Quicr/hactar/models/debug_board_case/debug-board-case-top.step

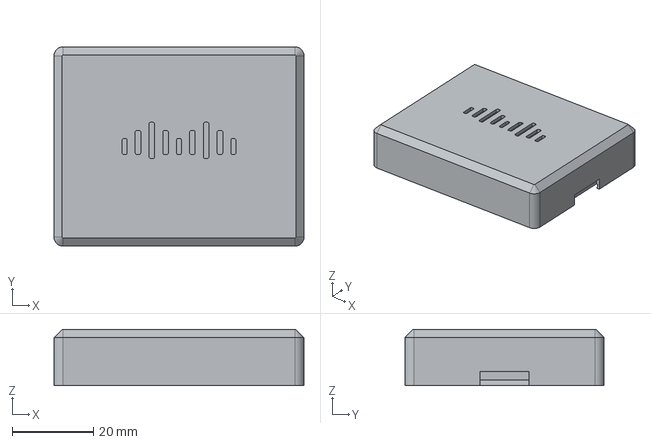
[picture p20: CAD file, 2026-09-29]
models/debug_board_case/debug-board-case-top.step
61.6 x 49.1 x 13.8 mm
