Quicr/hactar/models/ev15v2/ev15-case-topPad051.step

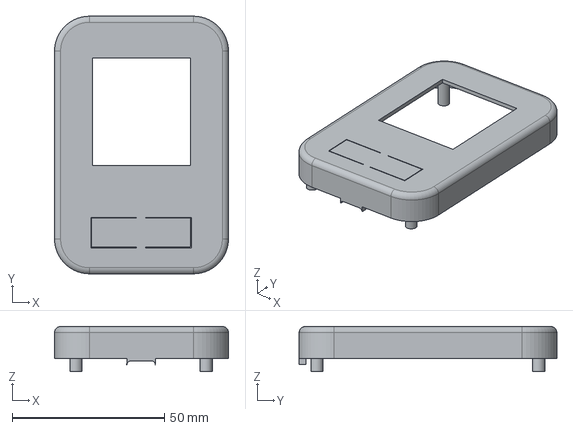
[picture p21: CAD file, 2026-01-12]
models/ev15v2/ev15-case-topPad051.step
57.2 x 84.7 x 14.8 mm
