Quicr/hactar/models/ev15v2/front-buttons-steps/ev15-case-front-button.step

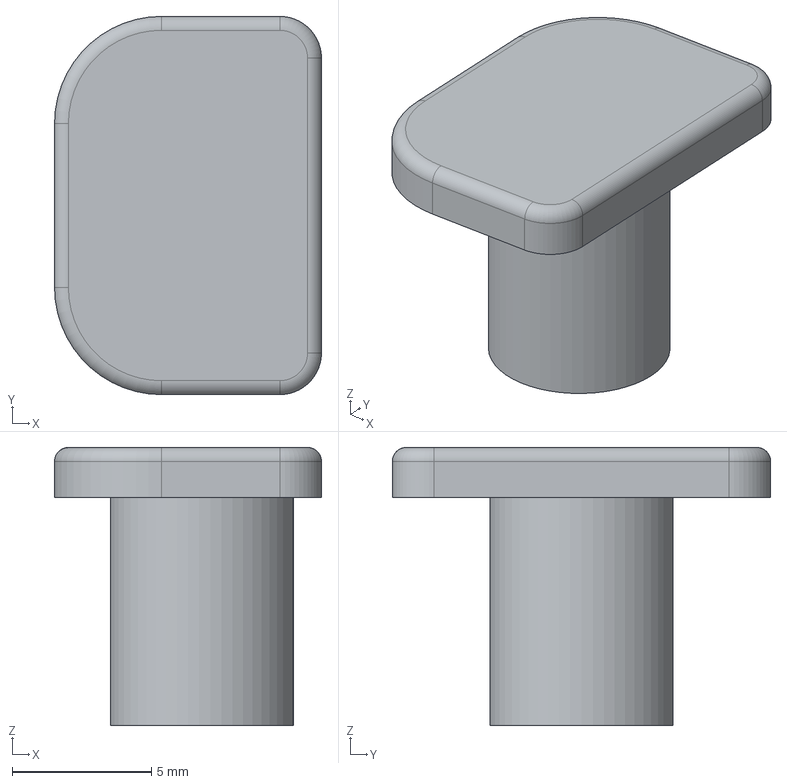
[picture p22: CAD file, 2025-11-21]
models/ev15v2/front-buttons-steps/ev15-case-front-button.step
9.60 x 13.6 x 10.0 mm
