Quicr/hactar/models/ev16/ev16-case-top.step

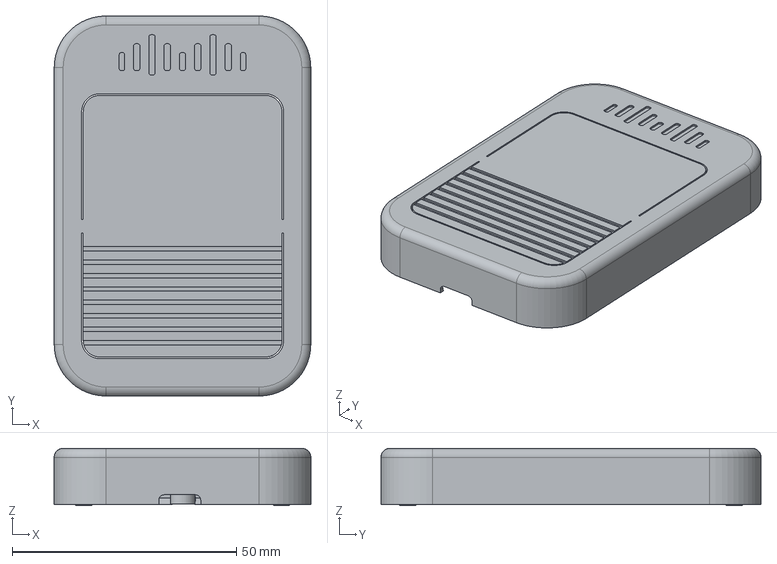
[picture p23: CAD file, 2026-01-12]
models/ev16/ev16-case-top.step
57.2 x 84.7 x 12.8 mm
