Quicr/hactar/models/ev17/ev17-case-top.step

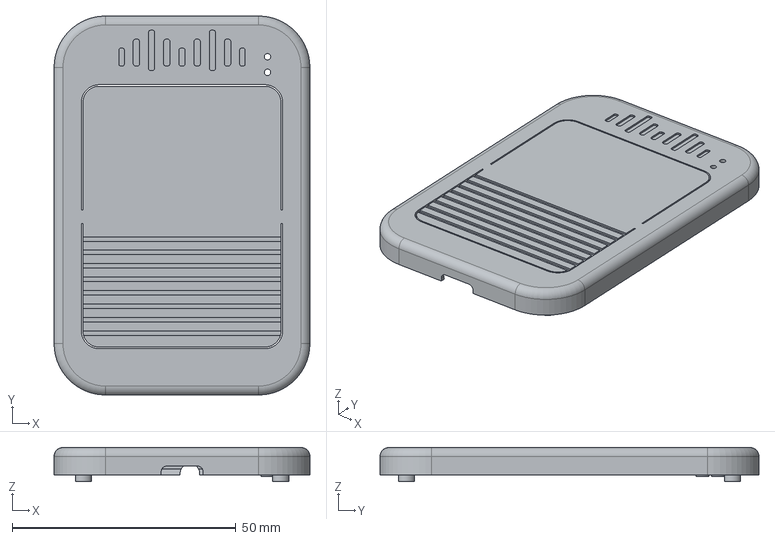
[picture p24: CAD file, 2026-05-21]
models/ev17/ev17-case-top.step
57.2 x 84.7 x 7.60 mm
