Quicr/hactar/models/ev19/keytar/ev19-keytar-case-inner-shelf.step

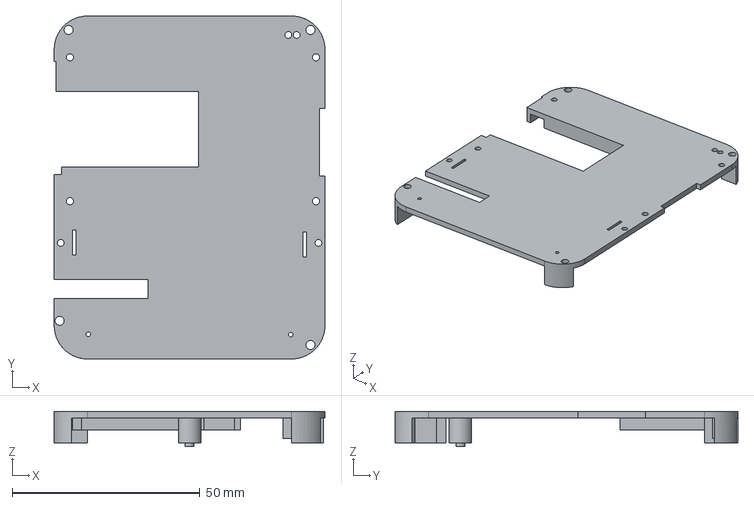
[picture p25: CAD file, 2026-09-29]
models/ev19/keytar/ev19-keytar-case-inner-shelf.step
72.1 x 91.3 x 9.40 mm
