Quicr/hactar/models/debug_board_case/debug-board-case-bottom.step

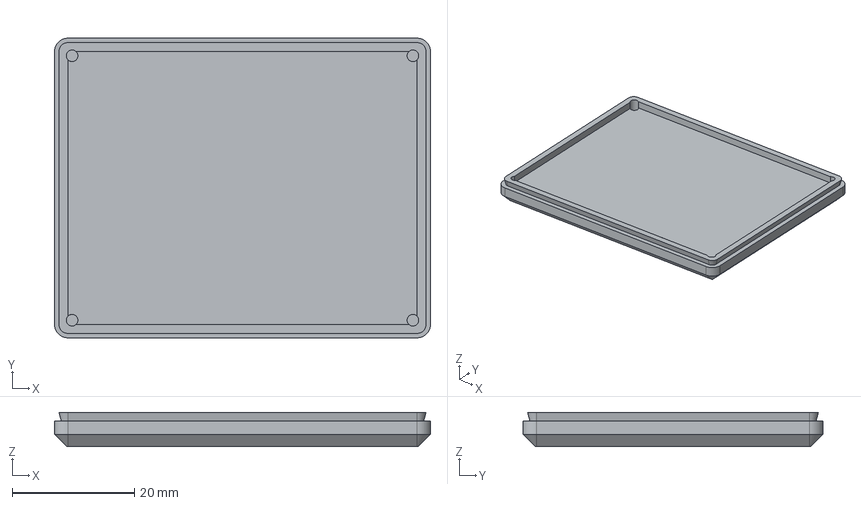
[picture p26: CAD file, 2026-09-29]
models/debug_board_case/debug-board-case-bottom.step
61.6 x 49.1 x 5.60 mm
