Quicr/hactar/models/ev15/brett_model/demo/ev15-case-screen-platform.step

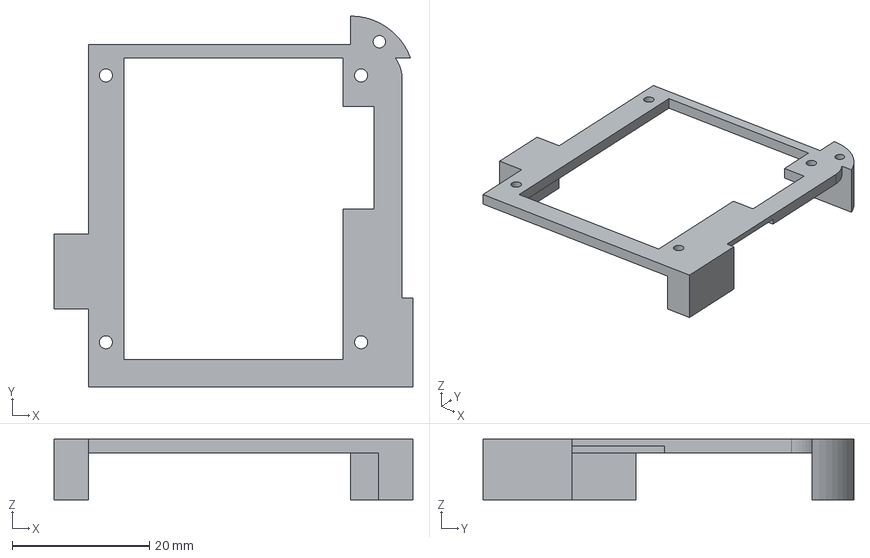
[picture p27: CAD file, 2025-11-21]
models/ev15/brett_model/demo/ev15-case-screen-platform.step
52.4 x 54.1 x 8.85 mm
