Quicr/hactar/models/ev15v2/front-buttons-steps/ev15-case-front-button-cap_+0.05mm.step

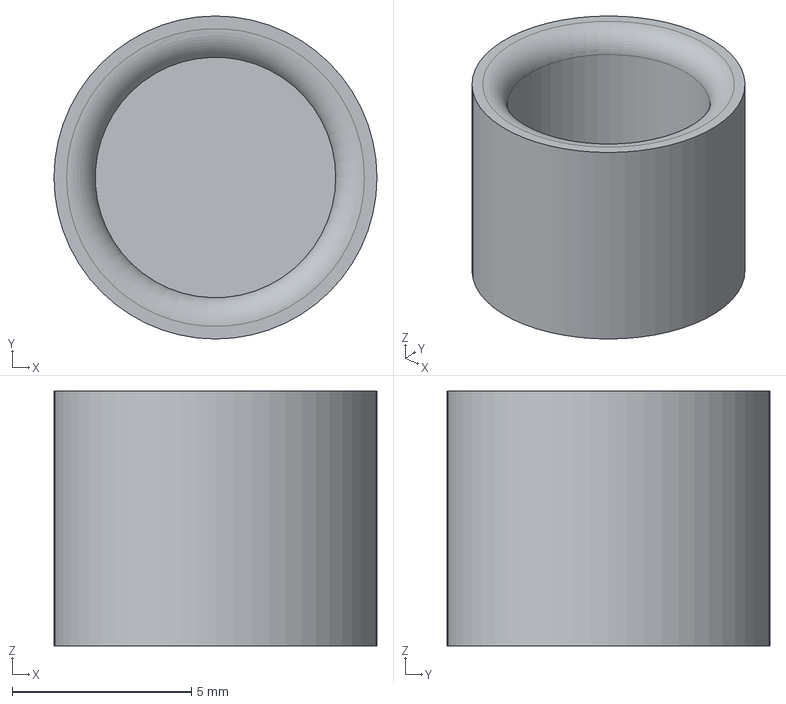
[picture p28: CAD file, 2025-11-21]
models/ev15v2/front-buttons-steps/ev15-case-front-button-cap_+0.05mm.step
9.00 x 9.00 x 7.10 mm
