Quicr/hactar/models/ev16/ev16-case-side-buttons.step

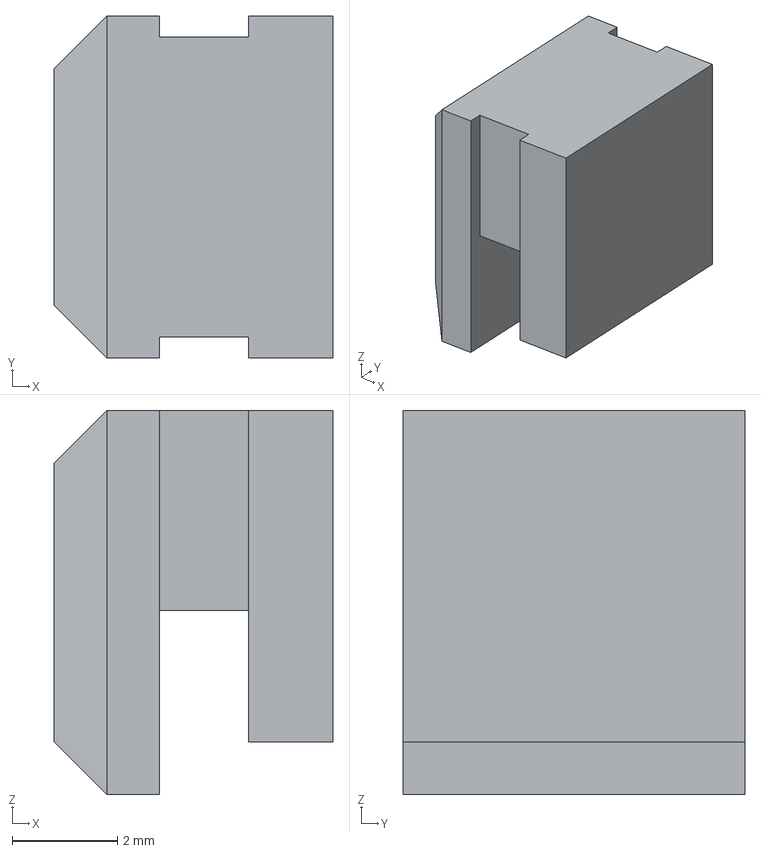
[picture p29: CAD file, 2026-01-12]
models/ev16/ev16-case-side-buttons.step
5.30 x 6.50 x 7.31 mm
