Quicr/hactar/models/ev17/ev17-case-side-buttons.step

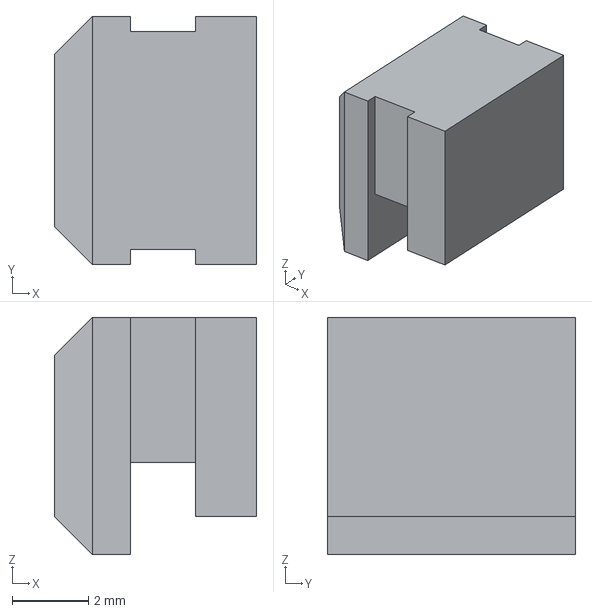
[picture p30: CAD file, 2026-05-21]
models/ev17/ev17-case-side-buttons.step
5.30 x 6.50 x 6.20 mm
