Quicr/hactar/models/ev19/keytar/ev19-keytar-case.FCStd

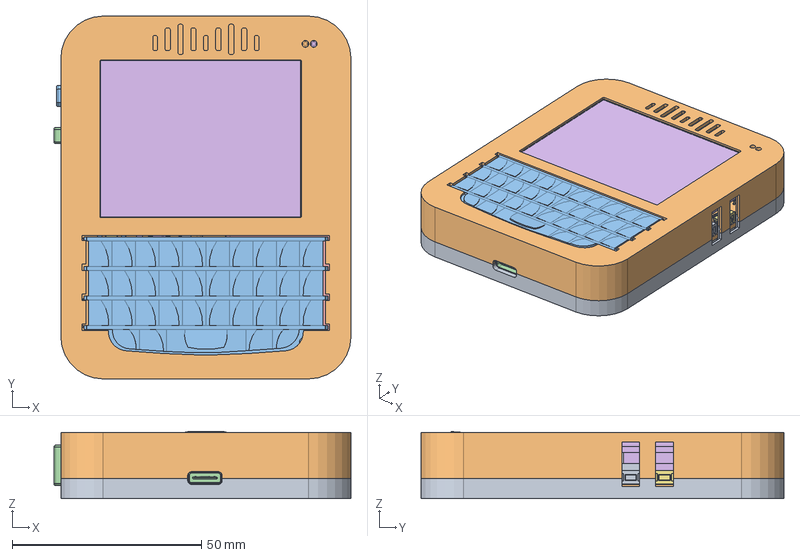
[picture p31: CAD file, 2026-09-29]
models/ev19/keytar/ev19-keytar-case.FCStd
78.5 x 95.9 x 17.7 mm
bottom
top
power-switch
side-button
screen-body
TSSOP-8_4.4x3mm_P0.65mm
C_0805_2012Metric
R_1206_3216Metric
R_0402_1005Metric
R_0402_1005Metric002
R_0402_1005Metric004
R_0402_1005Metric006
R_1206_3216Metric002
SOT-23
C_0402_1005Metric
C_0402_1005Metric002
R_1206_3216Metric004
ESP32-S3-WROOM-1
USB-C_SMD-TYPE-C-31-M-12
LQFP-48_7x7mm_P0.5mm
R_0402_1005Metric008
R_0402_1005Metric010
R_0402_1005Metric012
SOT-23-6
C_0402_1005Metric004
R_0402_1005Metric014
LED-ARRAY-SMD_4P-L1.6-W1.5-TL_NH-B1515RGBA
C_0402_1005Metric006
C_0402_1005Metric008
C_0805_2012Metric002
R_0402_1005Metric016
R_0402_1005Metric018
R_0402_1005Metric020
C_0402_1005Metric010
R_0402_1005Metric022
R_0402_1005Metric024
R_0402_1005Metric026
C_0402_1005Metric012
C_0805_2012Metric004
C_0402_1005Metric014
SOT-23-5
R_0402_1005Metric028
R_1206_3216Metric006
R_0402_1005Metric030
R_0402_1005Metric032
USB-C_SMD-TYPE-C-31-M-002
C_0805_2012Metric006
R_0402_1005Metric034
R_0402_1005Metric036
R_0402_1005Metric038
R_0603_1608Metric
R_0402_1005Metric040
R_0402_1005Metric042
R_0402_1005Metric044
R_0402_1005Metric046
C_0805_2012Metric008
R_0402_1005Metric048
C_0402_1005Metric016
R_1206_3216Metric008
R_0402_1005Metric050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
