Quicr/hactar/models/ev15/brett_model/demo/ev15-case-front-button.step

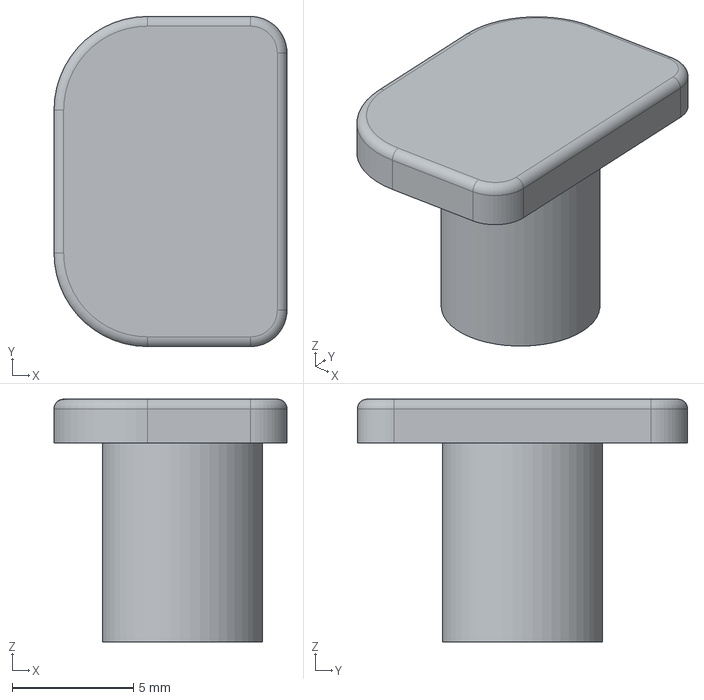
[picture p32: CAD file, 2025-11-21]
models/ev15/brett_model/demo/ev15-case-front-button.step
9.60 x 13.6 x 10.0 mm
