Quicr/hactar/models/ev17/ev17-case-bottom.step

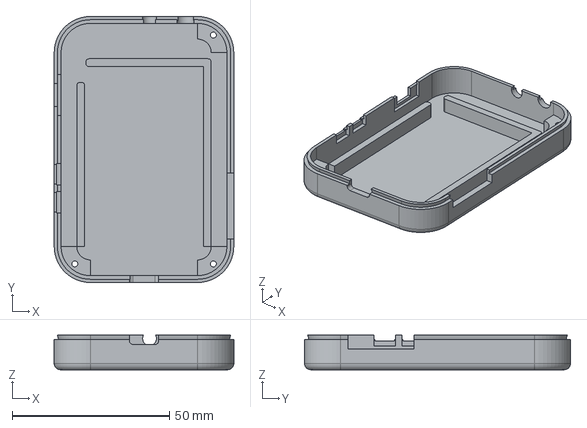
[picture p33: CAD file, 2026-05-21]
models/ev17/ev17-case-bottom.step
57.2 x 84.7 x 11.0 mm
