Quicr/hactar/models/ev19/keytar/ev19-keytar-case-top-debug-hole.step

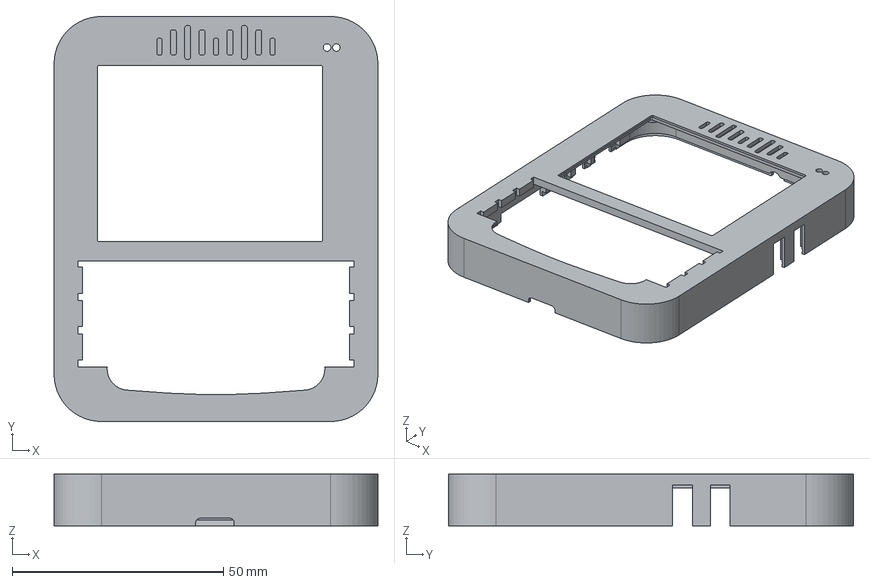
[picture p34: CAD file, 2026-09-29]
models/ev19/keytar/ev19-keytar-case-top-debug-hole.step
76.7 x 95.9 x 12.2 mm
