Quicr/hactar/models/ev17/ev17-case-power-switch.step

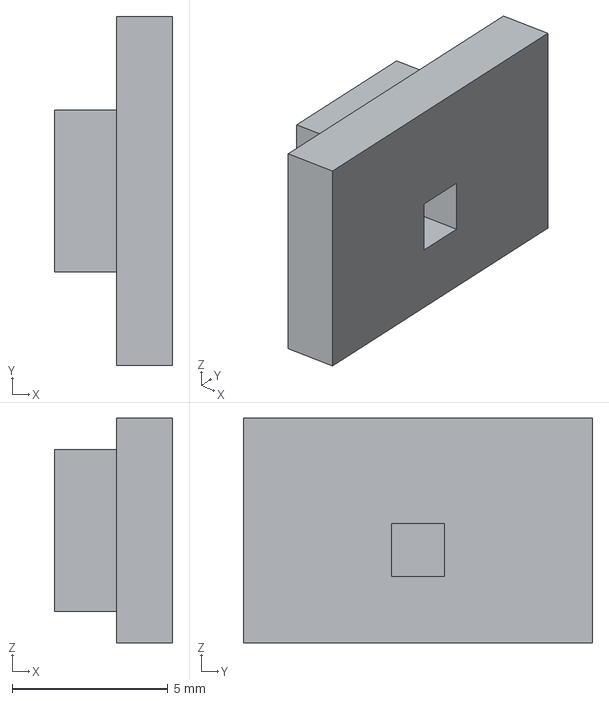
[picture p35: CAD file, 2026-05-21]
models/ev17/ev17-case-power-switch.step
3.80 x 11.2 x 7.21 mm
