Quicr/hactar/models/ev19/keytar/ev19-keytar-case-top.step

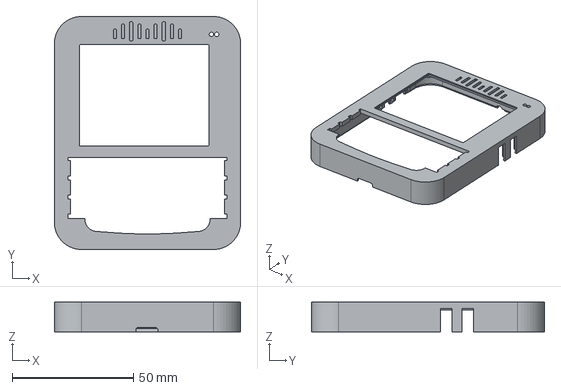
[picture p36: CAD file, 2026-09-29]
models/ev19/keytar/ev19-keytar-case-top.step
76.7 x 95.9 x 12.2 mm
