Quicr/hactar/models/ev19/keytar/ev19-keytar-case-bottom.step

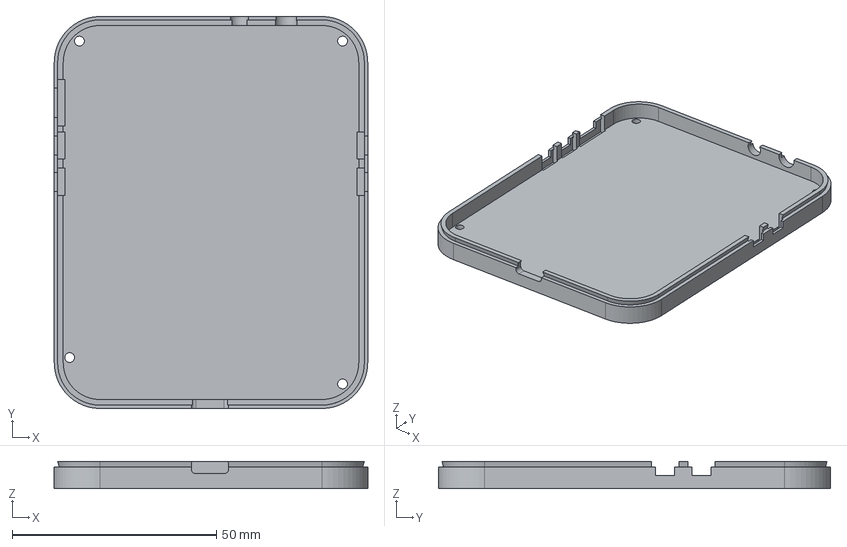
[picture p37: CAD file, 2026-09-29]
models/ev19/keytar/ev19-keytar-case-bottom.step
76.7 x 95.9 x 6.70 mm
