Quicr/hactar/models/ev19/keytar/ev19-keytar-case-power-switch.step

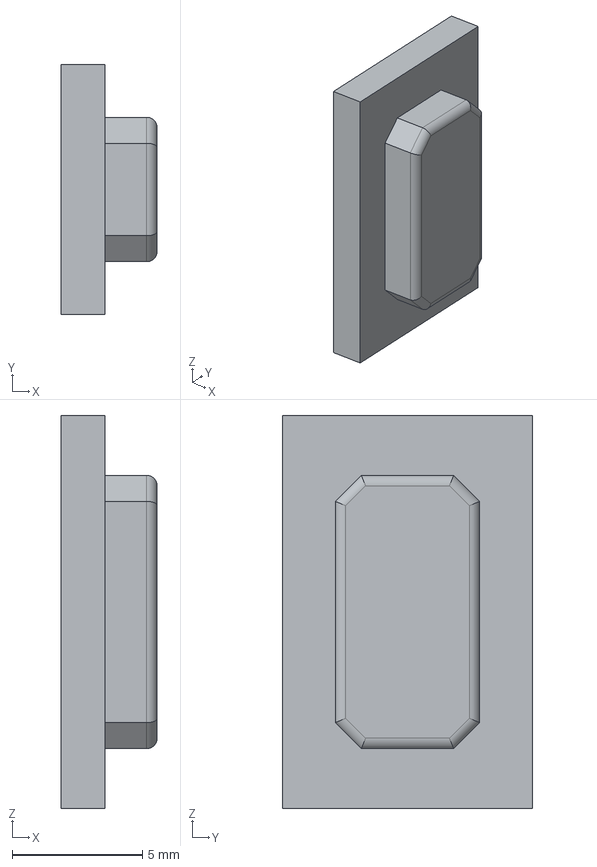
[picture p38: CAD file, 2026-09-29]
models/ev19/keytar/ev19-keytar-case-power-switch.step
3.70 x 9.60 x 15.1 mm
