Quicr/hactar/models/ev19/keytar/ev19-keytar-keyboard-shim.step

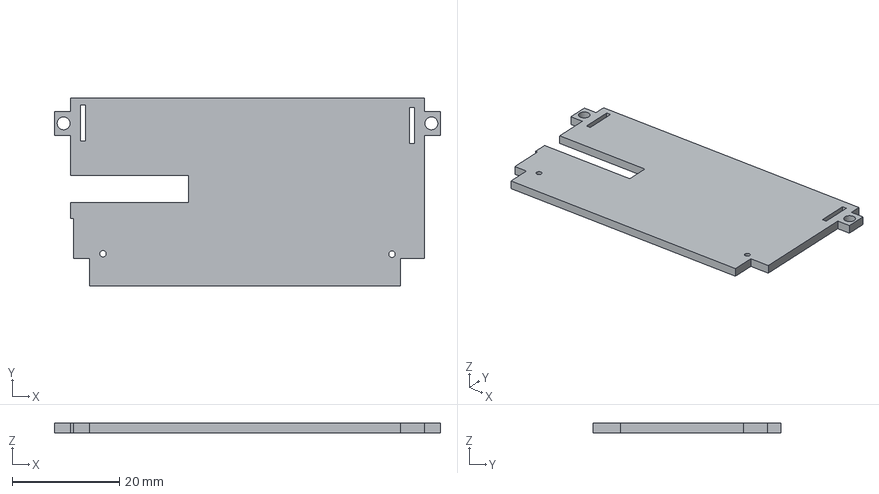
[picture p39: CAD file, 2026-09-29]
models/ev19/keytar/ev19-keytar-keyboard-shim.step
72.0 x 35.1 x 1.80 mm
