Quicr/hactar/firmware/mgmt/Core/Inc/io_control.h

#ifndef IO_CONTROL_H
#define IO_CONTROL_H

#include "main.h"
#include "uart_stream.h"

#define BAUD 115200


void PowerCycle(GPIO_TypeDef* port, uint16_t pin, uint32_t delay);
void HoldInReset(GPIO_TypeDef* port, uint16_t pin);
void ChangeToInput(GPIO_TypeDef* port, uint16_t pin);
void ChangeToOutput(GPIO_TypeDef* port, uint16_t pin);
void NormalAndNetUploadUartInit(uart_stream_t* stream, UART_HandleTypeDef* tx_uart);
void UIUploadStreamInit(uart_stream_t* stream, UART_HandleTypeDef* tx_uart);

#endif
