Quicr/hactar/firmware/net/components/serial/serial.cc

#include "serial.hh"
#include "logger.hh"
#include <random>

// This code is VERY specifically using espressif's serial event system which
// has many flaws, including but not limited to taking forever and less
// granularity.

Serial::Serial(const uart_port_t port,
               uart_dev_t& uart,
               const periph_interrupt_t intr_source,
               const uart_config_t uart_config,
               const int tx_pin,
               const int rx_pin,
               const int rts_pin,
               const int cts_pin,
               uint8_t& tx_buff,
               const uint32_t tx_buff_sz,
               uint8_t& rx_buff,
               const uint32_t rx_buff_sz,
               const uint32_t rx_rings,
               const uint32_t driver_tx_size,
               const uint32_t driver_rx_size,
               const uint32_t driver_queue_size,
               const bool use_queue_task,
               const bool use_slip) :
    SerialHandler(rx_rings, tx_buff, tx_buff_sz, rx_buff, rx_buff_sz, Transmit, this),
    port(port),
    uart(uart),
    read_handle(nullptr),
    uart_config(uart_config),
    tx_pin(tx_pin),
    rx_pin(rx_pin),
    rts_pin(rts_pin),
    cts_pin(cts_pin),
    driver_tx_size(driver_tx_size),
    driver_rx_size(driver_rx_size),
    driver_queue_size(driver_queue_size),
    use_queue_task(use_queue_task),
    queue(),
    uart_task_handle(nullptr)
{
}

void Serial::BeginEventTask(TaskHandle_t& read_handle)
{
    ESP_ERROR_CHECK(uart_param_config(port, &uart_config));
    ESP_ERROR_CHECK(uart_set_pin(port, tx_pin, rx_pin, rts_pin, cts_pin));

    this->read_handle = &read_handle;

    if (use_queue_task)
    {
        ESP_ERROR_CHECK(uart_driver_install(port, driver_rx_size, driver_tx_size, driver_queue_size,
                                            &queue, 0));
        xTaskCreate(QueueReadTask, "UART Queue Event Task", 4096, this, 20, &uart_task_handle);
    }
    else
    {
        ESP_ERROR_CHECK(uart_driver_install(port, driver_rx_size, driver_tx_size, driver_queue_size,
                                            nullptr, 0));
        xTaskCreate(ReadTask, "UART Read Event Task", 4096, this, 20, &uart_task_handle);
    }
}

Serial::~Serial()
{
    if (uart_task_handle)
    {
        vTaskDelete(uart_task_handle);
    }

    if (use_queue_task)
    {
        uart_driver_delete(port);
    }
}

void Serial::UpdateUnread(const uint16_t update)
{
    unread -= update;
}

void Serial::Transmit(void* arg)
{
    // TODO semaphores?
    Serial* serial = static_cast<Serial*>(arg);
    uart_write_bytes(serial->port, serial->tx_buff + serial->tx_read_idx, serial->num_to_send);
    serial->tx_free = true;
    serial->UpdateTx();
}

void Serial::ReadTask(void* arg)
{
    Serial* serial = static_cast<Serial*>(arg);

    while (true)
    {
        // Check if buffer is full
        if (serial->unread >= serial->rx_buff_sz)
        {
            vTaskDelay(1);
            continue;
        }

        // Calculate space to end of buffer (for contiguous write)
        int space_to_end = serial->rx_buff_sz - serial->rx_write_idx;
        // Calculate total free space in circular buffer
        int free_space = serial->rx_buff_sz - serial->unread;
        // Limit to contiguous space available
        int bytes_to_read = (space_to_end < free_space) ? space_to_end : free_space;

        if (bytes_to_read <= 0)
        {
            vTaskDelay(1);
            continue;
        }

        int num_bytes = uart_read_bytes(serial->port, serial->rx_buff + serial->rx_write_idx,
                                        bytes_to_read, 20 / portTICK_PERIOD_MS);

        if (num_bytes <= 0)
        {
            continue;
        }

        serial->rx_write_idx += num_bytes;
        if (serial->rx_write_idx >= serial->rx_buff_sz)
        {
            serial->rx_write_idx = 0;
        }
        serial->unread += num_bytes;
        xTaskNotifyGive(*serial->read_handle);
    }
}

void Serial::QueueReadTask(void* arg)
{
    Serial* serial = static_cast<Serial*>(arg);
    uart_event_t event;

    while (true)
    {
        if (!xQueueReceive(serial->queue, &event, portMAX_DELAY))
        {
            continue;
        }

        // NET_LOG_INFO("got event, size %d", event.size);

        switch (event.type)
        {
        case UART_DATA:
        {
            int bytes_remaining = event.size;
            int total_read = 0;

            while (bytes_remaining > 0)
            {
                // Check if buffer is full
                if (serial->unread >= serial->rx_buff_sz)
                {
                    ESP_LOGW("SerialPort", "RX buffer full, dropping %d bytes", bytes_remaining);
                    uart_flush_input(serial->port);
                    break;
                }

                // Calculate space to end of buffer (for contiguous write)
                int space_to_end = serial->rx_buff_sz - serial->rx_write_idx;
                // Calculate total free space in circular buffer
                int free_space = serial->rx_buff_sz - serial->unread;
                // Limit to contiguous space available
                int space_available = (space_to_end < free_space) ? space_to_end : free_space;
                // Don't read more than remaining bytes in event
                int bytes_to_read =
                    (space_available < bytes_remaining) ? space_available : bytes_remaining;

                if (bytes_to_read <= 0)
                {
                    break;
                }

                int num_bytes = uart_read_bytes(
                    serial->port, serial->rx_buff + serial->rx_write_idx, bytes_to_read, 0);

                if (num_bytes <= 0)
                {
                    break;
                }

                total_read += num_bytes;
                bytes_remaining -= num_bytes;
                serial->unread += num_bytes;

                serial->rx_write_idx += num_bytes;
                if (serial->rx_write_idx >= serial->rx_buff_sz)
                {
                    serial->rx_write_idx = 0;
                }
            }

            if (total_read > 0)
            {
                xTaskNotifyGive(*serial->read_handle);
            }

            break;
        }
        case UART_FIFO_OVF:
        {

            ESP_LOGW("SerialPort", "FIFO Overflow detected");
            uart_flush_input(serial->port);
            xQueueReset(serial->queue);
            break;
        }
        case UART_BUFFER_FULL:
        {
            ESP_LOGW("SerialPort", "Ring buffer full");
            uart_flush_input(serial->port);
            xQueueReset(serial->queue);
            break;
        }
        case UART_PARITY_ERR:
        {

            ESP_LOGE("SerialPort", "Parity error");
            break;
        }
        case UART_FRAME_ERR:
        {

            ESP_LOGE("SerialPort", "Frame error");
            break;
        }
        default:
        {
            ESP_LOGI("SerialPort", "Unhandled UART event type: %d", event.type);
            break;
        }
        }
    }
}
