Quicr/hactar/firmware/net/core/src/mgmt_link_handler.cc

#include "mgmt_link_handler.hh"
#include "efuse_burner.hh"
#include "esp_system.h"
#include "freertos/FreeRTOS.h"
#include "logger.hh"
#include "net.hh"
#include "net_mgmt_link.h"
#include "picoquic_utils.h"
#include "spdlog/spdlog.h"
#include "ui_net_link.hh"
#include <cstdint>

void MgmtLinkHandler::BlasterTask(void* arg)
{
    BlasterTaskContext* context = static_cast<BlasterTaskContext*>(arg);

    std::vector<uint8_t> blast_vec;
    constexpr uint8_t channel_id = (uint8_t)ui_net_link::Channel_Id::Ptt;
    TickType_t last_wake = xTaskGetTickCount();
    const TickType_t frequency = pdMS_TO_TICKS(20);
    if (context->blaster.enabled)
    {

        if (context->blaster.packet_size != blast_vec.size())
        {
            blast_vec.resize(context->blaster.packet_size);
            for (int i = 0; i < context->blaster.packet_size; ++i)
            {
                blast_vec[i] = 0;
            }
        }

        context->moq_context.PushAudioFrame(channel_id, blast_vec.data(), blast_vec.size(),
                                            context->runtime.curr_audio_isr_time);
    }

    xTaskDelayUntil(&last_wake, frequency);

    vTaskDelete(context->blaster.task_handle);
    context->blaster.task_handle = NULL;
}

MgmtLinkHandler::MgmtLinkHandler(Serial& mgmt_layer,
                                 Serial& ui_layer,
                                 Wifi& wifi,
                                 Storage& storage,
                                 ConfigState& config,
                                 Diagnostics& diagnostics,
                                 MoqContext& moq_context,
                                 Runtime& runtime_context) :
    serial(mgmt_layer),
    ui_serial(ui_layer),
    wifi(wifi),
    storage(storage),
    config(config),
    diagnostics(diagnostics),
    moq_context(moq_context),
    runtime_context(runtime_context),
    serial_read_handle(nullptr),
    serial_read_buffer(),
    serial_read_stack(),
    serial_read_semaphore(nullptr),
    serial_read_running(false),
    blaster_context(ui_layer, mgmt_layer, moq_context, runtime_context, diagnostics.blaster)
{
}

MgmtLinkHandler::~MgmtLinkHandler()
{
    serial_read_running = false;

    if (serial_read_handle)
    {
        // Tell the task to wake up so it can be stopped
        xTaskNotifyGive(serial_read_handle);
        xSemaphoreTake(serial_read_semaphore, portMAX_DELAY);
        serial_read_handle = nullptr;
    }

    if (serial_read_semaphore)
    {
        vSemaphoreDelete(serial_read_semaphore);
        serial_read_semaphore = nullptr;
    }

    if (serial_read_stack)
    {
        heap_caps_free(serial_read_stack);
        serial_read_stack = nullptr;
    }
}

void MgmtLinkHandler::Begin()
{
    CreateLinkPacketTask();
    serial.BeginEventTask(serial_read_handle);
}

void MgmtLinkHandler::CreateLinkPacketTask()
{
    NET_LOG_INFO("Creating mgmt link packet task");

    serial_read_semaphore = xSemaphoreCreateBinary();
    if (serial_read_semaphore == NULL)
    {
        esp_system_abort("Failed to allocate semaphore for mgmt link packet handler");
        return;
    }

    serial_read_stack =
        (StackType_t*)heap_caps_malloc(Stack_Size * sizeof(StackType_t), MALLOC_CAP_INTERNAL);
    if (serial_read_stack == NULL)
    {
        esp_system_abort("Failed to allocate stack for mgmt link packet handler");
        return;
    }

    serial_read_running = true;
    serial_read_handle = xTaskCreateStatic(LinkPacketTask, "mgmt link packet handler", Stack_Size,
                                           this, 10, serial_read_stack, &serial_read_buffer);

    NET_LOG_INFO("Created mgmt link packet handler Internal RAM left %ld",
                 heap_caps_get_free_size(MALLOC_CAP_INTERNAL));
}

void MgmtLinkHandler::LinkPacketTask(void* arg)
{
    MgmtLinkHandler* handler = static_cast<MgmtLinkHandler*>(arg);

    NET_LOG_INFO("Start mgmt link packet task");
    while (handler->serial_read_running)
    {
        ulTaskNotifyTake(pdTRUE, portMAX_DELAY);

        while (auto packet = handler->serial.Read())
        {
            switch (static_cast<CtlToNet>(packet->type))
            {
            case CtlToNet::Ping:
            {
                handler->serial.Reply(
                    static_cast<uint16_t>(NetToCtl::Pong),
                    std::span<const uint8_t>(packet->payload.data(), packet->length));
                break;
            }
            case CtlToNet::CircularPing:
            {
                // Forward to UI for circular path: MGMT -> NET -> UI -> MGMT
                handler->ui_serial.Reply(
                    static_cast<uint16_t>(ui_net_link::NetToUi::CircularPing),
                    std::span<const uint8_t>(packet->payload.data(), packet->length));
                break;
            }
            case CtlToNet::ClearStorage:
            {
                if (ESP_OK != handler->storage.Clear())
                {
                    handler->serial.ReplyError(static_cast<uint16_t>(NetToCtl::Error),
                                               "Storage clear failed");
                    break;
                }

                // Clear in-memory caches (NVS already wiped by storage.Clear())
                handler->config.moq_server_url.stored.clear();
                handler->config.user_id = 0;
                handler->config.user_name.stored.clear();
                handler->config.language.stored.clear();
                handler->config.channel_ns_json.stored.clear();
                handler->config.ai_query_ns_json.stored.clear();
                handler->config.ai_audio_response_ns_json.stored.clear();
                handler->config.ai_cmd_response_ns_json.stored.clear();

                // Clear in-memory namespace vectors
                handler->config.channel_ns.clear();
                handler->config.ai_query_ns.clear();
                handler->config.ai_audio_response_ns.clear();
                handler->config.ai_cmd_response_ns.clear();

                handler->wifi.ClearSavedSSIDs();

                handler->serial.Reply(static_cast<uint16_t>(NetToCtl::Ack),
                                      std::span<const uint8_t>{});
                break;
            }
            case CtlToNet::AddWifiSsid:
            {
                try
                {
                    std::string json_str((char*)packet->payload.data(), packet->length);
                    json wifi_json = json::parse(json_str);

                    if (!wifi_json.contains("ssid") || !wifi_json.contains("password"))
                    {
                        NET_LOG_ERROR("Add_Wifi: missing ssid or password field");
                        handler->serial.ReplyError(static_cast<uint16_t>(NetToCtl::Error),
                                                   "Missing ssid or password field");
                        break;
                    }

                    std::string ssid = wifi_json["ssid"].get<std::string>();
                    std::string password = wifi_json["password"].get<std::string>();

                    NET_LOG_INFO("Add_Wifi: ssid=%s", ssid.c_str());
                    handler->wifi.Connect(ssid, password);
                    handler->serial.Reply(static_cast<uint16_t>(NetToCtl::Ack),
                                          std::span<const uint8_t>{});
                }
                catch (const std::exception& ex)
                {
                    NET_LOG_ERROR("Add_Wifi: JSON parse error: %s", ex.what());
                    handler->serial.ReplyError(static_cast<uint16_t>(NetToCtl::Error),
                                               "Invalid JSON");
                }
                break;
            }
            case CtlToNet::GetWifiSsids:
            {
                json wifi_array = json::array();
                const std::vector<Wifi::ap_cred_t>& creds = handler->wifi.GetStoredCreds();
                for (const auto& cred : creds)
                {
                    json entry;
                    entry["ssid"] = std::string(cred.name, cred.name_len);
                    entry["password"] = std::string(cred.pwd, cred.pwd_len);
                    wifi_array.push_back(entry);
                }
                handler->serial.Reply(static_cast<uint16_t>(NetToCtl::WifiSsids),
                                      wifi_array.dump());
                break;
            }
            case CtlToNet::ClearWifiSsids:
            {
                handler->wifi.ClearSavedSSIDs();
                handler->serial.Reply(static_cast<uint16_t>(NetToCtl::Ack),
                                      std::span<const uint8_t>{});
                break;
            }
            case CtlToNet::SetRelayUrl:
            {
                std::string moq_url((char*)packet->payload.data(), packet->length);
                NET_LOG_INFO("Got moq url %d - %s", moq_url.length(), moq_url.c_str());

                if (moq_url.length() == 0)
                {
                    NET_LOG_INFO("Cleaning moq url because length is zero");
                    handler->config.moq_server_url.Clear();
                    handler->serial.Reply(static_cast<uint16_t>(NetToCtl::Ack),
                                          std::span<const uint8_t>{});
                    break;
                }
                handler->config.moq_server_url = moq_url;
                handler->serial.Reply(static_cast<uint16_t>(NetToCtl::Ack),
                                      std::span<const uint8_t>{});
                break;
            }
            case CtlToNet::GetRelayUrl:
            {
                std::string moq_url = handler->config.moq_server_url.Load();
                handler->serial.Reply(static_cast<uint16_t>(NetToCtl::RelayUrl), moq_url);
                break;
            }
            case CtlToNet::GetLoopback:
            {
                uint8_t mode = static_cast<uint8_t>(handler->diagnostics.loopback);
                handler->serial.Reply(static_cast<uint16_t>(NetToCtl::Loopback),
                                      std::span<const uint8_t>(&mode, 1));
                break;
            }
            case CtlToNet::SetLoopback:
            {
                if (packet->length < 1)
                {
                    handler->serial.ReplyError(static_cast<uint16_t>(NetToCtl::Error),
                                               "Missing loopback mode parameter");
                    break;
                }
                auto mode = static_cast<NetLoopbackMode>(packet->payload[0]);
                switch (mode)
                {
                case NetLoopbackMode::Off:
                    handler->diagnostics.loopback = NetLoopbackMode::Off;
                    NET_LOG_INFO("Loopback set to: off");
                    handler->serial.Reply(static_cast<uint16_t>(NetToCtl::Ack),
                                          std::span<const uint8_t>{});
                    break;
                case NetLoopbackMode::Raw:
                    handler->diagnostics.loopback = NetLoopbackMode::Raw;
                    NET_LOG_INFO("Loopback set to: raw");
                    handler->serial.ReplyError(static_cast<uint16_t>(NetToCtl::Ack),
                                               "Raw loopback not supported");
                    break;
                case NetLoopbackMode::Moq:
                    handler->diagnostics.loopback = NetLoopbackMode::Moq;
                    NET_LOG_INFO("Loopback set to: moq");
                    handler->serial.Reply(static_cast<uint16_t>(NetToCtl::Ack),
                                          std::span<const uint8_t>{});
                    break;
                default:
                    NET_LOG_WARN("Unknown loopback mode: %d", static_cast<int>(mode));
                    handler->serial.ReplyError(static_cast<uint16_t>(NetToCtl::Error),
                                               "Unknown loopback mode");
                    break;
                }
                break;
            }
            case CtlToNet::GetLogsEnabled:
            {
                uint8_t enabled = handler->diagnostics.logs_disabled ? 0 : 1;
                handler->serial.Reply(static_cast<uint16_t>(NetToCtl::LogsEnabled),
                                      std::span<const uint8_t>(&enabled, 1));
                break;
            }
            case CtlToNet::SetLogsEnabled:
            {
                if (packet->length < 1)
                {
                    handler->serial.ReplyError(static_cast<uint16_t>(NetToCtl::Error),
                                               "Missing logs enabled parameter");
                    break;
                }
                uint8_t enabled = packet->payload[0];
                if (enabled)
                {
                    handler->EnableLogging();
                }
                else
                {
                    handler->DisableLogging();
                }
                handler->serial.Reply(static_cast<uint16_t>(NetToCtl::Ack),
                                      std::span<const uint8_t>{});
                break;
            }
            case CtlToNet::SetLanguage:
            {
                std::string new_lang((char*)packet->payload.data(), packet->length);
                if (!ConfigState::IsValidLanguage(new_lang))
                {
                    NET_LOG_ERROR("Invalid language: %s", new_lang.c_str());
                    handler->serial.ReplyError(static_cast<uint16_t>(NetToCtl::Error),
                                               "Invalid language");
                    break;
                }
                handler->config.language = new_lang;
                NET_LOG_INFO("Language set to: %s", new_lang.c_str());
                handler->serial.Reply(static_cast<uint16_t>(NetToCtl::Ack),
                                      std::span<const uint8_t>{});
                handler->moq_context.UpdateAITracks(handler->config);
                handler->moq_context.UpdateChannelTracks(handler->config);
                break;
            }
            case CtlToNet::GetLanguage:
            {
                std::string lang = handler->config.language.Load();
                handler->serial.Reply(static_cast<uint16_t>(NetToCtl::Language), lang);
                break;
            }
            case CtlToNet::SetChannel:
            {
                std::string json_str((char*)packet->payload.data(), packet->length);
                auto parsed = ConfigState::JsonToNamespace(json_str);
                if (!parsed.has_value())
                {
                    NET_LOG_ERROR("Failed to parse channel namespace JSON");
                    handler->serial.ReplyError(static_cast<uint16_t>(NetToCtl::Error),
                                               "Invalid channel namespace JSON");
                    break;
                }

                handler->config.channel_ns = parsed.value();
                handler->config.channel_ns_json = json_str;
                NET_LOG_INFO("Channel namespace set (%zu parts)",
                             handler->config.channel_ns.size());
                handler->serial.Reply(static_cast<uint16_t>(NetToCtl::Ack),
                                      std::span<const uint8_t>{});
                handler->moq_context.UpdateChannelTracks(handler->config);
                break;
            }
            case CtlToNet::GetChannel:
            {
                handler->serial.Reply(static_cast<uint16_t>(NetToCtl::Channel),
                                      handler->config.channel_ns_json.Load());
                break;
            }
            case CtlToNet::GetAi:
            {
                json response;
                response["query"] = handler->config.ai_query_ns;
                response["audio"] = handler->config.ai_audio_response_ns;
                response["cmd"] = handler->config.ai_cmd_response_ns;
                handler->serial.Reply(static_cast<uint16_t>(NetToCtl::Ai), response.dump());
                break;
            }
            case CtlToNet::SetAi:
            {
                std::string json_str((char*)packet->payload.data(), packet->length);
                try
                {
                    json ai_config = json::parse(json_str);
                    if (!ai_config.is_object() || !ai_config.contains("query")
                        || !ai_config.contains("audio") || !ai_config.contains("cmd"))
                    {
                        NET_LOG_ERROR("AI config must be object with query, audio, cmd fields");
                        handler->serial.ReplyError(static_cast<uint16_t>(NetToCtl::Error),
                                                   "AI config requires query, audio, cmd fields");
                        break;
                    }

                    auto query_parsed = ConfigState::JsonToNamespace(ai_config["query"].dump());
                    auto audio_parsed = ConfigState::JsonToNamespace(ai_config["audio"].dump());
                    auto cmd_parsed = ConfigState::JsonToNamespace(ai_config["cmd"].dump());

                    if (!query_parsed || !audio_parsed || !cmd_parsed)
                    {
                        NET_LOG_ERROR("Failed to parse AI namespace arrays");
                        handler->serial.ReplyError(static_cast<uint16_t>(NetToCtl::Error),
                                                   "Invalid AI namespace arrays");
                        break;
                    }

                    handler->config.ai_query_ns = query_parsed.value();
                    handler->config.ai_audio_response_ns = audio_parsed.value();
                    handler->config.ai_cmd_response_ns = cmd_parsed.value();

                    handler->config.ai_query_ns_json = ai_config["query"].dump();
                    handler->config.ai_audio_response_ns_json = ai_config["audio"].dump();
                    handler->config.ai_cmd_response_ns_json = ai_config["cmd"].dump();

                    NET_LOG_INFO("AI namespaces set (query=%zu, audio=%zu, cmd=%zu parts)",
                                 handler->config.ai_query_ns.size(),
                                 handler->config.ai_audio_response_ns.size(),
                                 handler->config.ai_cmd_response_ns.size());
                    handler->serial.Reply(static_cast<uint16_t>(NetToCtl::Ack),
                                          std::span<const uint8_t>{});
                    handler->moq_context.UpdateAITracks(handler->config);
                }
                catch (const std::exception& ex)
                {
                    NET_LOG_ERROR("Failed to parse AI config JSON: %s", ex.what());
                    handler->serial.ReplyError(static_cast<uint16_t>(NetToCtl::Error),
                                               "Invalid AI config JSON");
                }
                break;
            }
            case CtlToNet::BlasterSend:
            {
                handler->serial.Reply(static_cast<uint16_t>(NetToCtl::Ack),
                                      std::span<const uint8_t>{});
                break;
            }
            case CtlToNet::GetBlaster:
            {
                const uint8_t get_blaster[3] = {
                    handler->diagnostics.blaster.enabled,
                    static_cast<uint8_t>(handler->diagnostics.blaster.packet_size & 0xFF),
                    static_cast<uint8_t>(handler->diagnostics.blaster.packet_size >> 8),
                };

                handler->serial.Reply(
                    static_cast<uint16_t>(NetToCtl::Blaster),
                    std::span<const uint8_t>(reinterpret_cast<const uint8_t*>(&get_blaster),
                                             sizeof(get_blaster)));

                break;
            }
            case CtlToNet::SetBlaster:
            {
                if (packet->length < 3)
                {
                    handler->serial.ReplyError(static_cast<uint16_t>(NetToCtl::Error),
                                               "SetBlaster requires {enabled:1}{size:2}");
                    break;
                }

                handler->diagnostics.blaster.enabled = packet->payload[0];

                const int16_t packet_size = (static_cast<uint16_t>(packet->payload[1]) & 0xFF)
                                          | (static_cast<uint16_t>(packet->payload[2] << 8));

                if (packet_size > 0)
                {
                    handler->diagnostics.blaster.packet_size = packet_size;
                }

                handler->serial.Reply(static_cast<uint16_t>(NetToCtl::Ack),
                                      std::span<const uint8_t>{});

                if (handler->diagnostics.blaster.enabled
                    && handler->diagnostics.blaster.task_handle == nullptr)
                {
                    xTaskCreate(BlasterTask, "Blaster task", 4096, (void*)&handler->blaster_context,
                                10, &handler->diagnostics.blaster.task_handle);
                }
                break;
            }
            case CtlToNet::BurnJtagEfuse:
            {
                const bool res = BurnDisableUSBJTagEFuse();
                if (res)
                {
                    handler->serial.Reply(static_cast<uint16_t>(NetToCtl::Ack),
                                          std::span<const uint8_t>{});
                }
                else
                {
                    handler->serial.ReplyError(static_cast<uint16_t>(NetToCtl::Error),
                                               "eFuse burn failed");
                }
                break;
            }
            case CtlToNet::GetUserId:
            {
                handler->config.user_id.Load();
                const uint64_t user_id = handler->config.user_id;
                handler->serial.Reply(
                    static_cast<uint16_t>(NetToCtl::UserId),
                    std::span<const uint8_t>(reinterpret_cast<const uint8_t*>(&user_id),
                                             sizeof(user_id)));
                break;
            }
            case CtlToNet::SetUserId:
            {
                if (packet->length != sizeof(handler->config.user_id.stored))
                {
                    break;
                }

                uint64_t user_id = 0;
                memcpy(&user_id, packet->payload.data(), sizeof(user_id));

                handler->config.user_id = user_id;

                NET_LOG_INFO("User id set to %lld", user_id);

                handler->serial.Reply(static_cast<uint16_t>(NetToCtl::Ack),
                                      std::span<const uint8_t>{});

                break;
            }
            case CtlToNet::GetUserName:
            {
                std::string username = handler->config.user_name.Load();
                handler->serial.Reply(static_cast<uint16_t>(NetToCtl::UserName), username);
                break;
            }
            case CtlToNet::SetUserName:
            {

                std::string new_name((char*)packet->payload.data(), packet->length);
                handler->config.user_name = new_name;
                NET_LOG_INFO("Language set to: %s", new_name.c_str());

                handler->serial.Reply(static_cast<uint16_t>(NetToCtl::Ack),
                                      std::span<const uint8_t>{});
                handler->moq_context.UpdateAITracks(handler->config);
                handler->moq_context.UpdateChannelTracks(handler->config);
                break;
            }
            default:
            {
                handler->serial.ReplyError(static_cast<uint16_t>(NetToCtl::Error),
                                           "Unknown packet type");
                NET_LOG_ERROR("Unknown packet type 0x%04x from mgmt", packet->type);
                break;
            }
            }
        }
    }

    xSemaphoreGive(handler->serial_read_semaphore);
    vTaskDelete(NULL);
}

void MgmtLinkHandler::DisableLogging()
{
    esp_log_level_set("*", ESP_LOG_NONE);
    auto logger = spdlog::get("MTC");
    if (logger)
    {
        diagnostics.last_spd_log_level = logger->level();
        logger->set_level(spdlog::level::level_enum::off);
    }

    debug_printf_suspend();
    diagnostics.logs_disabled = true;
}

void MgmtLinkHandler::EnableLogging()
{
    // Renable
    esp_log_level_set("*", ESP_LOG_MAX);

    auto logger = spdlog::get("MTC");
    if (logger)
    {
        logger->set_level(diagnostics.last_spd_log_level);
    }

    debug_printf_resume();
    diagnostics.logs_disabled = false;
}
