Quicr/hactar/firmware/net/components/moq_manager/moq_session.cc

#include "moq_session.hh"
#include "logger.hh"
#include "peripherals.hh"
#include "task_helpers.hh"
#include "utils.hh"
#include <driver/gpio.h>

using namespace moq;

extern uint64_t device_id;

Session::Session(const quicr::ClientConfig& cfg,
                 std::vector<std::shared_ptr<TrackReader>>& readers,
                 std::vector<std::shared_ptr<TrackWriter>>& writers) :
    Client(cfg),
    readers(readers),
    readers_task_handle(),
    readers_task_buffer(),
    readers_task_stack(),
    writers(writers),
    writers_task_handle(),
    writers_task_buffer(),
    writers_task_stack(),
    readers_mux(),
    writers_mux()
{
    StartTasks();
}

void Session::StopTracks() noexcept
{
    for (const auto& reader : readers)
    {
        if (reader)
        {
            UnsubscribeTrack(reader);
        }
    }

    for (const auto& writer : writers)
    {
        if (writer)
        {
            UnpublishTrack(writer);
        }
    }
}

void Session::StartTasks() noexcept
{
    task_helpers::Start_PSRAM_Task(PublishTrackTask, this, "Publish Tracks task",
                                   writers_task_handle, writers_task_buffer, &writers_task_stack,
                                   8192, 10);
    task_helpers::Start_PSRAM_Task(SubscribeTrackTask, this, "Subscribe Tracks task",
                                   readers_task_handle, readers_task_buffer, &readers_task_stack,
                                   8192, 10);
}

void Session::StatusChanged(Status status)
{
    switch (status)
    {
    case Status::kReady:
        Logger::Log(Logger::Level::Info, "MOQ Connection ready");
        gpio_set_level(NET_LED_G, 1);
        gpio_set_level(NET_LED_B, 0);
        break;
    case Status::kConnecting:
        break;
    case Status::kPendingServerSetup:
        Logger::Log(Logger::Level::Info, "MOQ Connection connected and now pending server setup");
        break;
    default:
        Logger::Log(Logger::Level::Error, "MOQ Connection failed: %i", static_cast<int>(status));
        break;
    }
}

std::shared_ptr<TrackWriter> Session::Writer(const size_t id) noexcept
{
    if (id > writers.size())
    {
        NET_LOG_ERROR("ERROR, writer with id %ld does not exist", id);
        return nullptr;
    }

    return writers[id];
}

void Session::PublishTrackTask(void* params)
{
    // TODO use a mutex to try and subscribe/publish
    // as I could remove them from the list or update them.
    Session* session = static_cast<Session*>(params);

    while (true)
    {
        while (session->GetStatus() != moq::Session::Status::kReady)
        {
            vTaskDelay(100 / portTICK_PERIOD_MS);
            continue;
        }

        {
            std::lock_guard<std::mutex> _(session->writers_mux);

            for (auto& writer : session->writers)
            {
                if (!writer)
                {
                    continue;
                }

                const auto can_publish = [&] {
                    const auto status = writer->GetStatus();
                    return status == moq::TrackWriter::Status::kOk
                        || status == moq::TrackWriter::Status::kSubscriptionUpdated
                        || status == moq::TrackWriter::Status::kNewGroupRequested;
                };

                // Writer is publishing
                if (can_publish())
                {
                    continue;
                }

                session->PublishTrack(writer);

                while (!can_publish())
                {
                    vTaskDelay(300 / portTICK_PERIOD_MS);
                }
            }
        }

        vTaskDelay(5000 / portTICK_PERIOD_MS);
    }

    vTaskDelete(nullptr);
}

void Session::SubscribeTrackTask(void* params)
{
    // TODO use a mutex to try and subscribe/publish
    // as I could remove them from the list or update them.

    // TODO notifier that awakes the thread when a new sub or pub is available
    Session* session = static_cast<Session*>(params);

    while (true)
    {
        while (session->GetStatus() != moq::Session::Status::kReady)
        {
            vTaskDelay(100 / portTICK_PERIOD_MS);
            continue;
        }

        {
            std::lock_guard<std::mutex> _(session->readers_mux);

            for (auto& reader : session->readers)
            {
                if (!reader)
                {
                    continue;
                }

                // Reader is subscribed
                if (reader->GetStatus() == moq::TrackReader::Status::kOk)
                {
                    continue;
                }

                session->SubscribeTrack(reader);

                while (reader->GetStatus() != moq::TrackReader::Status::kOk)
                {
                    vTaskDelay(300 / portTICK_PERIOD_MS);
                }
            }
        }

        vTaskDelay(5000 / portTICK_PERIOD_MS);
    }

    vTaskDelete(nullptr);
}

// TODO delete when moq session can be reused instead of reinstantiated
std::unique_lock<std::mutex> Session::GetReaderLock()
{
    return std::unique_lock<std::mutex>(readers_mux);
}

std::unique_lock<std::mutex> Session::GetWriterLock()
{
    return std::unique_lock<std::mutex>(writers_mux);
}
