Quicr/hactar/firmware/net/core/src/peripherals.cc

#include "peripherals.hh"
#include "driver/gpio.h"
#include "net.hh"

extern QueueHandle_t uart_queue;

void InitializeGPIO()
{
    gpio_config_t io_conf = {};
    // Debug init
    io_conf.intr_type = GPIO_INTR_DISABLE;
    io_conf.mode = GPIO_MODE_OUTPUT;
    io_conf.pin_bit_mask = NET_DEBUG_MASK;
    io_conf.pull_down_en = (gpio_pulldown_t)0;
    io_conf.pull_up_en = (gpio_pullup_t)0;
    gpio_config(&io_conf);
}

void IntitializeLEDs()
{
    gpio_config_t io_conf = {};
    // LED init
    io_conf.intr_type = GPIO_INTR_DISABLE;
    io_conf.mode = GPIO_MODE_OUTPUT;
    io_conf.pin_bit_mask = LED_MASK;
    io_conf.pull_down_en = (gpio_pulldown_t)0;
    io_conf.pull_up_en = (gpio_pullup_t)0;
    gpio_config(&io_conf);

    // Yellow on startup (no wifi/moq)
    gpio_set_level(NET_LED_R, 0);
    gpio_set_level(NET_LED_G, 0);
    gpio_set_level(NET_LED_B, 1);
}

void InitializeUIReadyISR(gpio_isr_t isr_handler)
{

    gpio_config_t io_conf = {.pin_bit_mask = UI_READY_MASK,
                             .mode = GPIO_MODE_INPUT,
                             .pull_up_en = GPIO_PULLUP_DISABLE,
                             .pull_down_en = GPIO_PULLDOWN_DISABLE,
                             .intr_type = GPIO_INTR_POSEDGE};
    gpio_config(&io_conf);
    gpio_install_isr_service(0);
    gpio_isr_handler_add(UI_READY, isr_handler, (void*)UI_READY);
}

void IntitializePWM()
{
    constexpr ledc_timer_t ledc_timer = LEDC_TIMER_0;
    constexpr ledc_mode_t ledc_mode = LEDC_LOW_SPEED_MODE;
    constexpr int ledc_io = NET_LED_R;
    constexpr ledc_channel_t ledc_channel = LEDC_CHANNEL_0;
    constexpr ledc_timer_bit_t ledc_duty_res = LEDC_TIMER_8_BIT;
    constexpr int ledc_duty = 255;
    constexpr int ledc_freq = 8000;

    // Prepare and then apply the LEDC PWM timer configuration
    ledc_timer_config_t ledc_timer_c = {.speed_mode = ledc_mode,
                                        .duty_resolution = ledc_duty_res,
                                        .timer_num = ledc_timer,
                                        .freq_hz = ledc_freq, // Set output frequency at 4 kHz
                                        .clk_cfg = LEDC_AUTO_CLK,
                                        .deconfigure = false};
    ESP_ERROR_CHECK(ledc_timer_config(&ledc_timer_c));

    // Prepare and then apply the LEDC PWM channel configuration
    ledc_channel_config_t ledc_channel_c = {.gpio_num = ledc_io,
                                            .speed_mode = ledc_mode,
                                            .channel = ledc_channel,
                                            .intr_type = LEDC_INTR_DISABLE,
                                            .timer_sel = ledc_timer,
                                            .duty = 0, // Set duty to 0%
                                            .hpoint = 0,
                                            .sleep_mode = LEDC_SLEEP_MODE_NO_ALIVE_NO_PD,
                                            .flags = {.output_invert = 0}};
    ESP_ERROR_CHECK(ledc_channel_config(&ledc_channel_c));
    // Set duty to 50%
    ESP_ERROR_CHECK(ledc_set_duty(ledc_mode, ledc_channel, ledc_duty));
    // Update duty to apply the new value
    ESP_ERROR_CHECK(ledc_update_duty(ledc_mode, ledc_channel));
}
