Quicr/hactar/firmware/net/core/src/mot_track_reader.cc

// SPDX-FileCopyrightText: Copyright (c) 2024 Cisco Systems
// SPDX-License-Identifier: BSD-2-Clause

#include "../inc/moq_track_reader.hh"
#include "utils.hh"

using namespace moqt;

void
TrackReader::ObjectReceived(const quicr::ObjectHeaders& headers, quicr::BytesSpan data)
{
    std::string msg(data.begin(), data.end());
    SPDLOG_INFO("Object Received: {0}", to_hex(data));
}

void
TrackReader::StatusChanged(quicr::SubscribeTrackHandler::Status status)
{
    switch (status) {
        case Status::kOk: {
            if (auto track_alias = GetTrackAlias(); track_alias.has_value()) {
                SPDLOG_INFO("Reader:Track {0} with alias: {1} is ready to read",
                            Stringify(GetFullTrackName()),
                            track_alias.value());
            }
        } break;
        default:
            break;
    }
}
