Quicr/hactar/firmware/ui/ui.ioc

Mcu.UserName=STM32F405RGTx
PA10.GPIO_Label=UI_RX1_MGMT
PA10.Signal=USART1_RX
PA13.Signal=SYS_JTMS-SWDIO
PA14.Signal=SYS_JTCK-SWCLK
PA15.GPIO_Label=I2S_DACLRC
PA15.Signal=I2S3_WS
PA2.GPIO_Label=UI_TX2_NET
PA2.Signal=USART2_TX
PA3.GPIO_Label=UI_RX2_NET
PA3.Signal=USART2_RX
PA4.GPIO_Label=MIC_IO
PA4.Signal=GPIO_Input
PA5.GPIO_Label=SPI1_CLK
PA5.Signal=SPI1_SCK
PA6.Signal=SPI1_MISO
PA7.GPIO_Label=SPI1_MOSI
PA7.Signal=SPI1_MOSI
PA9.GPIO_Label=UI_TX1_MGMT
PA9.Signal=USART1_TX
PB1.GPIO_Label=PLUG_DETECT
PB1.Signal=GPIO_Input
PB10.GPIO_Label=VOLUME_UP
PB10.Signal=GPIO_Input
PB11.GPIO_Label=KB_COL1
PB11.Signal=GPIO_Output
PB12.GPIO_Label=KB_COL2
PB12.Signal=GPIO_Output
PB13.GPIO_Label=KB_COL3
PB13.Signal=GPIO_Output
PB14.GPIO_Label=KB_COL4
PB14.Signal=GPIO_Output
PB15.GPIO_Label=KB_ROW7
PB15.Signal=GPIO_Input
PB2.GPIO_Label=UI_BOOT1
PB2.Signal=GPIO_Input
PB4.GPIO_Label=I2S_ADCDAT
PB4.Signal=I2S3_ext_SD
PB5.GPIO_Label=I2S_DACDAT
PB5.Signal=I2S3_SD
PB6.GPIO_Label=UI_SCL1
PB6.Signal=I2C1_SCL
PB7.GPIO_Label=UI_SDA1
PB7.Signal=I2C1_SDA
PB8.GPIO_Label=DISP_DC
PB8.Signal=GPIO_Output
PB9.GPIO_Label=DISP_RST
PB9.Signal=GPIO_Output
PC0.GPIO_Label=PTT_BTN
PC0.Signal=GPIO_Input
PC1.GPIO_Label=PTT_AI_BTN
PC1.Signal=GPIO_Input
PC10.GPIO_Label=I2S_BCLK
PC10.Signal=I2S3_CK
PC11.GPIO_Label=UI_STAT
PC11.Signal=GPIO_Output
PC12.GPIO_Label=KB_ROW4
PC12.Signal=GPIO_Input
PC13-ANTI_TAMP.GPIO_Label=KB_ROW5
PC13-ANTI_TAMP.Signal=GPIO_Input
PC14-OSC32_IN.GPIO_Label=KB_ROW6
PC14-OSC32_IN.Signal=GPIO_Input
PC15-OSC32_OUT.GPIO_Label=KB_COL5
PC15-OSC32_OUT.Signal=GPIO_Output
PC2.GPIO_Label=UI_READY
PC2.Signal=GPIO_Output
PC3.GPIO_Label=NET_READY
PC3.Signal=GPXTI3
PC4.GPIO_Label=KB_ROW1
PC4.Signal=GPIO_Input
PC5.GPIO_Label=KB_ROW2
PC5.Signal=GPIO_Input
PC6.GPIO_Label=UI_LED_R
PC6.Signal=S_TIM3_CH1
PC7.GPIO_Label=UI_LED_G
PC7.Signal=S_TIM3_CH2
PC8.GPIO_Label=UI_LED_B
PC8.Signal=S_TIM3_CH3
PC9.GPIO_Label=KB_ROW3
PC9.Signal=GPIO_Input
PD2.GPIO_Label=VOLUME_DOWN
PD2.Signal=GPIO_Input
PH0-OSC_IN.GPIO_Label=MCLK
PH0-OSC_IN.Signal=RCC_OSC_IN
PH1-OSC_OUT.GPIO_Label=NC
PH1-OSC_OUT.Signal=RCC_OSC_OUT
