Quicr/hactar/firmware/ui/src/app_main.cc

#include "app_main.hh"
#include "audio_chip.hh"
#include "audio_codec.hh"
#include "button.hh"
#include "config_storage.hh"
#include "constants.hh"
#include "keyboard.hh"
#include "keyboard_display.hh"
#include "led_control.hh"
#include "link_packet_handler.hh"
#include "link_packet_t.hh"
#include "logger.hh"
#include "main.h"
#include "protector.hh"
#include "renderer.hh"
#include "screen.hh"
#include "serial.hh"
#include "stm32f4xx_hal_gpio.h"
#include "tools.hh"
#include "ui_mgmt_link.h"
#include "ui_net_link.hh"
#include "wave_signal_generator.hh"
#include <cmox_crypto.h>
#include <cmox_init.h>
#include <cmox_low_level.h>
#include <sframe/sframe.h>
#include <stm32f4xx_hal.h>
#include <cstdint>
#include <cstring>
#include <random>
#include <span>

// Forward declare
inline void CheckPTT(Protector& protector, const UiLoopbackMode loopback_mode);
inline void CheckPTTAI(Protector& protector, const UiLoopbackMode loopback_mode);
inline void SendAudio(Protector& protector,
                      const ui_net_link::Channel_Id channel_id,
                      bool last,
                      const UiLoopbackMode loopback_mode);
inline void HandleMedia(link_packet_t* packet);
inline void HandleAiResponse(link_packet_t* packet);

// Handlers
extern UART_HandleTypeDef huart1;
extern UART_HandleTypeDef huart2;

extern SPI_HandleTypeDef hspi1;
extern I2C_HandleTypeDef hi2c1;
extern I2S_HandleTypeDef hi2s3;
extern TIM_HandleTypeDef htim2;
extern TIM_HandleTypeDef htim3;
extern TIM_HandleTypeDef htim4;
extern TIM_HandleTypeDef htim5;
extern RNG_HandleTypeDef hrng;

// Global variables that need to exist for hardware callbacks
UiLoopbackMode loopback_mode = UiLoopbackMode::Off;
AudioTransmitMode audio_transmit_mode = AudioTransmitMode::Net;
AudioReceiveMode audio_receive_mode = AudioReceiveMode::Headphones;

// Buffer allocations
static constexpr uint16_t net_ui_serial_tx_buff_sz = 2048;
uint8_t net_ui_serial_tx_buff[net_ui_serial_tx_buff_sz] = {0};
static constexpr uint16_t net_ui_serial_rx_buff_sz = 2048;
uint8_t net_ui_serial_rx_buff[net_ui_serial_rx_buff_sz] = {0};
static constexpr uint16_t net_ui_serial_num_rx_packets = 7;

static constexpr uint16_t mgmt_ui_serial_tx_buff_sz = 1024;
uint8_t mgmt_ui_serial_tx_buff[mgmt_ui_serial_tx_buff_sz] = {0};
static constexpr uint16_t mgmt_ui_serial_rx_buff_sz = 1024;
uint8_t mgmt_ui_serial_rx_buff[mgmt_ui_serial_rx_buff_sz] = {0};
static constexpr uint16_t mgmt_ui_serial_num_rx_packets = 1;

static AudioChip audio_chip(hi2s3, hi2c1);

static Serial net_serial(&huart2,
                         net_ui_serial_num_rx_packets,
                         *net_ui_serial_tx_buff,
                         net_ui_serial_tx_buff_sz,
                         *net_ui_serial_rx_buff,
                         net_ui_serial_rx_buff_sz,
                         false);
static Serial mgmt_serial(&huart1,
                          mgmt_ui_serial_num_rx_packets,
                          *mgmt_ui_serial_tx_buff,
                          mgmt_ui_serial_tx_buff_sz,
                          *mgmt_ui_serial_rx_buff,
                          mgmt_ui_serial_rx_buff_sz,
                          false);

#if 0
// Screen screen(hspi1,
//               DISP_CS_GPIO_Port,
//               DISP_CS_Pin,
//               DISP_DC_GPIO_Port,
//               DISP_DC_Pin,
//               DISP_RST_GPIO_Port,
//               DISP_RST_Pin,
//               DISP_BL_GPIO_Port,
//               DISP_BL_Pin,
//               Screen::Orientation::flipped_portrait);
//
// GPIO_TypeDef* col_ports[Keyboard::Q10_Cols] = {
//     KB_COL1_GPIO_Port, KB_COL2_GPIO_Port, KB_COL3_GPIO_Port, KB_COL4_GPIO_Port,
//     KB_COL5_GPIO_Port,
// };
//
// uint16_t col_pins[Keyboard::Q10_Cols] = {
//     KB_COL1_Pin, KB_COL2_Pin, KB_COL3_Pin, KB_COL4_Pin, KB_COL5_Pin,
// };
//
// GPIO_TypeDef* row_ports[Keyboard::Q10_Rows] = {
//     KB_ROW1_GPIO_Port, KB_ROW2_GPIO_Port, KB_ROW3_GPIO_Port, KB_ROW4_GPIO_Port,
//     KB_ROW5_GPIO_Port, KB_ROW6_GPIO_Port, KB_ROW7_GPIO_Port,
// };

// uint16_t row_pins[Keyboard::Q10_Rows] = {
//     KB_ROW1_Pin, KB_ROW2_Pin, KB_ROW3_Pin, KB_ROW4_Pin, KB_ROW5_Pin, KB_ROW6_Pin, KB_ROW7_Pin,
// }
// ;

// static constexpr uint16_t kb_ring_buff_sz = 5;
// RingBuffer<uint8_t> kb_buff(kb_ring_buff_sz);
//
// Keyboard keyboard(col_ports, col_pins, row_ports, row_pins, kb_buff, 150, 150);
#endif

volatile bool sleeping = true;
volatile bool error = false;

constexpr uint32_t Expected_Flags = (1 << Timer_Flags_Count) - 1;
uint32_t flags = Expected_Flags;

enum class Ptt_Btn_State
{
    Released = 0,
    Pressed,
    Releasing,
    Last_Send,
};

Ptt_Btn_State ptt_state;
Ptt_Btn_State ptt_ai_state;

Button ptt(PTT_BTN_GPIO_Port, PTT_BTN_Pin, Button::Polarity::High, 0, 0, 10000, 10000);
Button mic_ptt(MIC_IO_GPIO_Port, MIC_IO_Pin, Button::Polarity::Low, 0, 0, 10000, 10000);
Button ptt_ai(PTT_AI_BTN_GPIO_Port, PTT_AI_BTN_Pin, Button::Polarity::High, 0, 0, 10000, 10000);
Button volume_up(VOLUME_UP_GPIO_Port, VOLUME_UP_Pin, Button::Polarity::High, 20, 100, 200, 200);
Button
    volume_down(VOLUME_DOWN_GPIO_Port, VOLUME_DOWN_Pin, Button::Polarity::High, 20, 100, 200, 200);

int app_main()
{
    HAL_TIM_Base_Start_IT(&htim2);

    mgmt_serial.StartReceive();

    // Enable TLV logging via MGMT serial
    Logger::SetLogSender([](uint16_t type, const uint8_t* data, size_t len) {
        mgmt_serial.Reply(type, std::span<const uint8_t>(data, len));
    });

    uint32_t ticks_ms = 0;
    ConfigStorage config_storage(hi2c1);
    Protector protector(config_storage);
    // Renderer renderer(screen, keyboard);

    audio_chip.Init();
    audio_chip.StartI2S();

    // Test in case the audio chip settings change and something looks suspicious
    CountNumAudioInterrupts(audio_chip, sleeping);

    // InitScreen(screen);
    Leds(LOW, LOW, LOW);
    net_serial.StartReceive();

    // TODO remove once we have a proper loading screen/view implementation
    const uint32_t loading_done_timeout = HAL_GetTick();
    bool done_booting = false;

    UI_LOG_INFO("Starting main loop");

    uint32_t volume_button_press_ms = 0;
    constexpr uint32_t Volume_Button_Debounce_ms = 200;

    uint32_t sleep_timeout = 0;

    while (1)
    {
        Heartbeat(UI_LED_R_GPIO_Port, UI_LED_R_Pin);

        if (!done_booting && HAL_GetTick() - loading_done_timeout >= 2000)
        {
            // renderer.ChangeView(Renderer::View::Chat);
            done_booting = true;
        }

        while (sleeping)
        {
            // LowPowerMode();
            __NOP();
        }

        ticks_ms = HAL_GetTick();
        sleep_timeout = ticks_ms;

        if (error)
        {
            // Error("Main loop", "Flags did not match expected");
        }

        if (volume_up.ShortPress() || volume_up.RepeatedPress())
        {
            audio_chip.DACVolumeAdjust(1);
            UI_LOG_INFO("DACVolume up %d", (int)audio_chip.DACVolume());
        }
        else if (volume_up.DoublePress())
        {
            audio_chip.ADCVolumeAdjust(1);
            UI_LOG_INFO("Mic Preamp up %d", (int)audio_chip.ADCVolume());
        }

        if (volume_down.ShortPress() || volume_down.RepeatedPress())
        {
            audio_chip.DACVolumeAdjust(-1);
            UI_LOG_INFO("DACVolume down %d", (int)audio_chip.DACVolume());
        }
        else if (volume_down.DoublePress())
        {
            audio_chip.ADCVolumeAdjust(-1);
            UI_LOG_INFO("Mic Preamp down %d", (int)audio_chip.ADCVolume());
        }

        CheckPTT(protector, loopback_mode);
        CheckPTTAI(protector, loopback_mode);

        // HandleKeypress(screen, keyboard, net_serial, protector);

        HandleNetLinkPackets(net_serial, mgmt_serial, protector, audio_chip, audio_receive_mode);
        HandleMgmtLinkPackets(mgmt_serial, net_serial, config_storage, audio_chip, loopback_mode,
                              audio_transmit_mode, audio_receive_mode);

        // renderer.Render(ticks_ms);
        // TODO remove?
        RaiseFlag(Rx_Audio_Companded);
        RaiseFlag(Rx_Audio_Transmitted);
        RaiseFlag(Draw_Complete);

        sleeping = true;
    }

    return 0;
}

inline void RaiseFlag(Timer_Flags flag)
{
    if (error)
    {
        return;
    }
    flags |= 1 << flag;
}

inline void LowerFlag(Timer_Flags flag)
{
    flags &= ~(1 << flag);
}

inline void LowPowerMode()
{
    HAL_SuspendTick();
    HAL_PWR_EnterSLEEPMode(PWR_MAINREGULATOR_ON, PWR_SLEEPENTRY_WFE);
}

inline void WakeUp()
{

    HAL_ResumeTick();
    sleeping = false;
}

inline void CheckFlags()
{
    if (flags != Expected_Flags)
    {
        error = true;
    }
    else
    {
        flags = 0;
    }
}

inline void AudioCallback()
{
    audio_chip.ISRCallback();

    CheckFlags();
    WakeUp();

    HAL_GPIO_WritePin(UI_READY_GPIO_Port, UI_READY_Pin, HIGH);
    HAL_TIM_Base_Start_IT(&htim3);

    RaiseFlag(Audio_Interrupt);
}

void CheckPTT(Protector& protector, const UiLoopbackMode loopback_mode)
{
    static bool pressed = false;

    if ((ptt.IsHeld() || mic_ptt.IsHeld()))
    {
        pressed = true;
        SendAudio(protector, ui_net_link::Channel_Id::Ptt, false, loopback_mode);
    }
    else if (pressed && (!ptt.IsHeld() && !ptt.IsHeld()))
    {
        pressed = false;
        SendAudio(protector, ui_net_link::Channel_Id::Ptt, true, loopback_mode);
    }
}

void CheckPTTAI(Protector& protector, const UiLoopbackMode loopback_mode)
{

    // Send talk start and sot packets
    if (HAL_GPIO_ReadPin(PTT_AI_BTN_GPIO_Port, PTT_AI_BTN_Pin) == GPIO_PIN_SET
        && ptt_ai_state != Ptt_Btn_State::Pressed)
    {
        HAL_TIM_Base_Stop(&htim5);
        ptt_ai_state = Ptt_Btn_State::Pressed;
        LedBOn();
    }
    else if (HAL_GPIO_ReadPin(PTT_AI_BTN_GPIO_Port, PTT_AI_BTN_Pin) == GPIO_PIN_RESET
             && ptt_ai_state == Ptt_Btn_State::Pressed)
    {
        ptt_ai_state = Ptt_Btn_State::Releasing;
        HAL_TIM_Base_Start_IT(&htim5);
    }

    if (ptt_ai_state == Ptt_Btn_State::Pressed || ptt_ai_state == Ptt_Btn_State::Releasing)
    {
        SendAudio(protector, ui_net_link::Channel_Id::Ptt_Ai, false, loopback_mode);
    }

    if (ptt_ai_state == Ptt_Btn_State::Last_Send)
    {
        SendAudio(protector, ui_net_link::Channel_Id::Ptt_Ai, true, loopback_mode);
        ptt_ai_state = Ptt_Btn_State::Released;
    }
}

void ConstructPacketHeader(link_packet_t& message_packet,
                           const ui_net_link::Channel_Id channel_id,
                           const bool last,
                           uint32_t& offset)
{
    offset = 0;
}

void SendAudioToMgmt(link_packet_t& packet, const bool last)
{

    static bool first = true;

    if (first)
    {
        first = false;
        mgmt_serial.Reply(static_cast<uint16_t>(UiToCtl::AudioStart), std::span<const uint8_t>{});
    }

    packet.type = static_cast<uint16_t>(UiToCtl::AudioFrame);
    mgmt_serial.Write(packet);

    if (last)
    {
        first = true;
        mgmt_serial.Reply(static_cast<uint16_t>(UiToCtl::AudioEnd), std::span<const uint8_t>{});
    }
}

void SendAudio(Protector& protector,
               const ui_net_link::Channel_Id channel_id,
               bool last,
               const UiLoopbackMode loopback_mode)
{
    const uint16_t* mic_in_ptr = audio_chip.MicInPtr();
    if (loopback_mode == UiLoopbackMode::Raw)
    {
        uint16_t* hp_out_ptr = audio_chip.HpOutPtr();

        for (size_t i = 0; i < constants::Audio_Buffer_Sz; ++i)
        {
            hp_out_ptr[i] = mic_in_ptr[i];
        }
    }

    link_packet_t audio_packet;

    uint32_t offset = 0;
    audio_packet.payload[offset] = static_cast<uint8_t>(channel_id);
    offset += sizeof(uint8_t);
    // UI_LOG_INFO("Channel id %d", (int)audio_packet.payload[0]);

    static constexpr uint32_t audio_size = constants::Audio_Phonic_Sz;
    if (channel_id == ui_net_link::Channel_Id::Ptt)
    {
        audio_packet.payload[offset] = static_cast<uint8_t>(ui_net_link::MessageType::Media);
        offset += sizeof(uint8_t);

        audio_packet.payload[offset] = static_cast<uint8_t>(last);
        offset += sizeof(uint8_t);

        memcpy(audio_packet.payload.data() + offset, &audio_size, sizeof(uint32_t));
        offset += sizeof(uint32_t);
    }
    else if (channel_id == ui_net_link::Channel_Id::Ptt_Ai)
    {
        audio_packet.payload[offset] = static_cast<uint8_t>(ui_net_link::MessageType::AIRequest);
        offset += sizeof(uint8_t);

        uint32_t request_id = 0;
        memcpy(audio_packet.payload.data() + offset, &request_id, sizeof(uint32_t));
        offset += sizeof(uint32_t);

        audio_packet.payload[offset] = static_cast<uint8_t>(last);
        offset += sizeof(uint8_t);

        memcpy(audio_packet.payload.data() + offset, &audio_size, sizeof(uint32_t));
        offset += sizeof(uint32_t);
    }
    else
    {
        UI_LOG_ERROR("Channel Id %d does not exist", static_cast<int>(channel_id));
        return;
    }

    audio_packet.length = offset + constants::Audio_Phonic_Sz;

    AudioCodec::ALawCompand(mic_in_ptr, constants::Audio_Buffer_Sz,
                            audio_packet.payload.data() + offset, constants::Audio_Phonic_Sz, true,
                            constants::Stereo);

    if (loopback_mode == UiLoopbackMode::Alaw)
    {
        AudioCodec::ALawExpand(audio_packet.payload.data() + offset, constants::Audio_Phonic_Sz,
                               audio_chip.HpOutPtr(), constants::Audio_Buffer_Sz, constants::Stereo,
                               true);
    }

    if (!protector.TryProtect(&audio_packet))
    {
        UI_LOG_ERROR("Failed to encrypt audio packet");
        return;
    }

    switch (audio_transmit_mode)
    {
    case AudioTransmitMode::Net:
    {
        audio_packet.type = static_cast<uint16_t>(ui_net_link::UiToNet::AudioFrame);

        net_serial.Write(audio_packet);
        break;
    }
    case AudioTransmitMode::Mgmt:
    {
        SendAudioToMgmt(audio_packet, last);

        break;
    }
    case AudioTransmitMode::Both:
    {
        SendAudioToMgmt(audio_packet, last);

        audio_packet.type = static_cast<uint16_t>(ui_net_link::UiToNet::AudioFrame);
        net_serial.Write(audio_packet);
        break;
    }
    }

    if (loopback_mode == UiLoopbackMode::Sframe)
    {
        if (!protector.TryUnprotect(&audio_packet))
        {
            UI_LOG_ERROR("Failed to unprotect sframe loopback");
            return;
        }

        AudioCodec::ALawExpand(audio_packet.payload.data() + offset, constants::Audio_Phonic_Sz,
                               audio_chip.HpOutPtr(), constants::Audio_Buffer_Sz, constants::Stereo,
                               true);
    }
}

void HAL_UARTEx_RxEventCallback(UART_HandleTypeDef* huart, uint16_t size)
{
    // UI_LOG_ERROR("rx %u", size);
    if (huart->Instance == Serial::UART(&net_serial)->Instance)
    {
        Serial::RxISR(&net_serial, size);
    }
    else if (huart->Instance == Serial::UART(&mgmt_serial)->Instance)
    {
        Serial::RxISR(&mgmt_serial, size);
    }
}

void HAL_UART_TxCpltCallback(UART_HandleTypeDef* huart)
{
    if (huart->Instance == Serial::UART(&net_serial)->Instance)
    {
        Serial::TxISR(&net_serial);
        RaiseFlag(Rx_Audio_Transmitted);
    }
    else if (huart->Instance == Serial::UART(&mgmt_serial)->Instance)
    {
        Serial::TxISR(&mgmt_serial);
    }
}

void HAL_UART_ErrorCallback(UART_HandleTypeDef* huart)
{
    if (huart->Instance == Serial::UART(&net_serial)->Instance)
    {
        net_serial.Stop();
        net_serial.StartReceive();
    }
}

void HAL_UART_AbortReceiveCpltCallback(UART_HandleTypeDef* huart)
{
    if (huart->Instance == Serial::UART(&net_serial)->Instance)
    {
        net_serial.StartReceive();
    }
}

void HAL_I2SEx_TxRxHalfCpltCallback(I2S_HandleTypeDef* hi2s)
{
    UNUSED(hi2s);
    AudioCallback();
}

void HAL_I2SEx_TxRxCpltCallback(I2S_HandleTypeDef* hi2s)
{
    UNUSED(hi2s);
    AudioCallback();
}

void HAL_SPI_TxCpltCallback(SPI_HandleTypeDef* hspi)
{
    UNUSED(hspi);
}

void HAL_TIM_PeriodElapsedCallback(TIM_HandleTypeDef* htim)
{
    // Keyboard timer callback!
    if (htim->Instance == TIM2)
    {
        // keyboard.Scan(HAL_GetTick());
        ptt.Update(HAL_GetTick());
        mic_ptt.Update(HAL_GetTick());
        ptt_ai.Update(HAL_GetTick());
        volume_up.Update(HAL_GetTick());
        volume_down.Update(HAL_GetTick());
    }
    else if (htim->Instance == TIM3)
    {
        // LedBToggle();
        HAL_GPIO_WritePin(UI_READY_GPIO_Port, UI_READY_Pin, LOW);
        HAL_TIM_Base_Stop_IT(&htim3);
    }
    else if (htim->Instance == TIM4)
    {
        // Turn off ptt
        HAL_TIM_Base_Stop(&htim4);
        ptt_state = Ptt_Btn_State::Last_Send;
        LedGOff();
    }
    else if (htim->Instance == TIM5)
    {
        HAL_TIM_Base_Stop(&htim5);
        ptt_ai_state = Ptt_Btn_State::Last_Send;
        LedBOff();
    }
}

#ifdef USE_FULL_ASSERT
/**
 * @brief  Reports the name of the source file and the source line number
 *         where the assert_param error has occurred.
 * @param  file: pointer to the source file name
 * @param  line: assert_param error line source number
 * @retval None
 */
void assert_failed(uint8_t* file, uint32_t line)
{
    /* USER CODE BEGIN 6 */
    /* User can add his own implementation to report the file name and line number,
        e.g.: printf("Wrong parameters value: file %s on line %d\r\n", file, line) */
    /* USER CODE END 6 */
}
#endif /* USE_FULL_ASSERT */

void Error(const char* who, const char* why)
{
    // Disable interrupts
    UI_LOG_ERROR("Error has occurred; who: %s; why: %s", who, why);
    audio_chip.StopI2S();
    net_serial.Stop();

    HAL_GPIO_WritePin(UI_LED_B_GPIO_Port, UI_LED_B_Pin, HIGH);
    HAL_GPIO_WritePin(UI_LED_G_GPIO_Port, UI_LED_G_Pin, HIGH);
    while (1)
    {
        HAL_GPIO_TogglePin(UI_LED_R_GPIO_Port, UI_LED_R_Pin);
        HAL_Delay(1000);
    }
}
