Quicr/hactar/firmware/ui/Core/Inc/main.h

#define KB_ROW5_Pin GPIO_PIN_13
#define KB_ROW5_GPIO_Port GPIOC
#define KB_ROW6_Pin GPIO_PIN_14
#define KB_ROW6_GPIO_Port GPIOC
#define KB_COL5_Pin GPIO_PIN_15
#define KB_COL5_GPIO_Port GPIOC
#define MCLK_Pin GPIO_PIN_0
#define MCLK_GPIO_Port GPIOH
#define NC_Pin GPIO_PIN_1
#define NC_GPIO_Port GPIOH
#define PTT_BTN_Pin GPIO_PIN_0
#define PTT_BTN_GPIO_Port GPIOC
#define PTT_AI_BTN_Pin GPIO_PIN_1
#define PTT_AI_BTN_GPIO_Port GPIOC
#define UI_READY_Pin GPIO_PIN_2
#define UI_READY_GPIO_Port GPIOC
#define NET_READY_Pin GPIO_PIN_3
#define NET_READY_GPIO_Port GPIOC
#define UI_TX2_NET_Pin GPIO_PIN_2
#define UI_TX2_NET_GPIO_Port GPIOA
#define UI_RX2_NET_Pin GPIO_PIN_3
#define UI_RX2_NET_GPIO_Port GPIOA
#define MIC_IO_Pin GPIO_PIN_4
#define MIC_IO_GPIO_Port GPIOA
#define SPI1_CLK_Pin GPIO_PIN_5
#define SPI1_CLK_GPIO_Port GPIOA
#define SPI1_MOSI_Pin GPIO_PIN_7
#define SPI1_MOSI_GPIO_Port GPIOA
#define KB_ROW1_Pin GPIO_PIN_4
#define KB_ROW1_GPIO_Port GPIOC
#define KB_ROW2_Pin GPIO_PIN_5
#define KB_ROW2_GPIO_Port GPIOC
#define PLUG_DETECT_Pin GPIO_PIN_1
#define PLUG_DETECT_GPIO_Port GPIOB
#define UI_BOOT1_Pin GPIO_PIN_2
#define UI_BOOT1_GPIO_Port GPIOB
#define VOLUME_UP_Pin GPIO_PIN_10
#define VOLUME_UP_GPIO_Port GPIOB
#define KB_COL1_Pin GPIO_PIN_11
#define KB_COL1_GPIO_Port GPIOB
#define KB_COL2_Pin GPIO_PIN_12
#define KB_COL2_GPIO_Port GPIOB
#define KB_COL3_Pin GPIO_PIN_13
#define KB_COL3_GPIO_Port GPIOB
#define KB_COL4_Pin GPIO_PIN_14
#define KB_COL4_GPIO_Port GPIOB
#define KB_ROW7_Pin GPIO_PIN_15
#define KB_ROW7_GPIO_Port GPIOB
#define UI_LED_R_Pin GPIO_PIN_6
#define UI_LED_R_GPIO_Port GPIOC
#define UI_LED_G_Pin GPIO_PIN_7
#define UI_LED_G_GPIO_Port GPIOC
#define UI_LED_B_Pin GPIO_PIN_8
#define UI_LED_B_GPIO_Port GPIOC
#define KB_ROW3_Pin GPIO_PIN_9
#define KB_ROW3_GPIO_Port GPIOC
#define UI_TX1_MGMT_Pin GPIO_PIN_9
#define UI_TX1_MGMT_GPIO_Port GPIOA
#define UI_RX1_MGMT_Pin GPIO_PIN_10
#define UI_RX1_MGMT_GPIO_Port GPIOA
#define I2S_DACLRC_Pin GPIO_PIN_15
#define I2S_DACLRC_GPIO_Port GPIOA
#define I2S_BCLK_Pin GPIO_PIN_10
#define I2S_BCLK_GPIO_Port GPIOC
#define UI_STAT_Pin GPIO_PIN_11
#define UI_STAT_GPIO_Port GPIOC
#define KB_ROW4_Pin GPIO_PIN_12
#define KB_ROW4_GPIO_Port GPIOC
#define VOLUME_DOWN_Pin GPIO_PIN_2
#define VOLUME_DOWN_GPIO_Port GPIOD
#define I2S_ADCDAT_Pin GPIO_PIN_4
#define I2S_ADCDAT_GPIO_Port GPIOB
#define I2S_DACDAT_Pin GPIO_PIN_5
#define I2S_DACDAT_GPIO_Port GPIOB
#define UI_SCL1_Pin GPIO_PIN_6
#define UI_SCL1_GPIO_Port GPIOB
#define UI_SDA1_Pin GPIO_PIN_7
#define UI_SDA1_GPIO_Port GPIOB
#define DISP_DC_Pin GPIO_PIN_8
#define DISP_DC_GPIO_Port GPIOB
#define DISP_RST_Pin GPIO_PIN_9
#define DISP_RST_GPIO_Port GPIOB
