Quicr/hactar/firmware/ui/src/led_control.cc

#include "led_control.hh"

void LedR(GPIO_PinState state)
{
    HAL_GPIO_WritePin(UI_LED_R_GPIO_Port, UI_LED_R_Pin, state);
}

void LedG(GPIO_PinState state)
{
    HAL_GPIO_WritePin(UI_LED_G_GPIO_Port, UI_LED_G_Pin, state);
}

void LedB(GPIO_PinState state)
{
    HAL_GPIO_WritePin(UI_LED_B_GPIO_Port, UI_LED_B_Pin, state);
}

void Leds(GPIO_PinState r, GPIO_PinState g, GPIO_PinState b)
{
    HAL_GPIO_WritePin(UI_LED_R_GPIO_Port, UI_LED_R_Pin, r);
    HAL_GPIO_WritePin(UI_LED_G_GPIO_Port, UI_LED_G_Pin, g);
    HAL_GPIO_WritePin(UI_LED_B_GPIO_Port, UI_LED_B_Pin, b);
}

void LedROn()
{
    HAL_GPIO_WritePin(UI_LED_R_GPIO_Port, UI_LED_R_Pin, LOW);
}

void LedROff()
{
    HAL_GPIO_WritePin(UI_LED_R_GPIO_Port, UI_LED_R_Pin, HIGH);
}

void LedRToggle()
{
    HAL_GPIO_TogglePin(UI_LED_R_GPIO_Port, UI_LED_R_Pin);
}

void LedBOn()
{
    HAL_GPIO_WritePin(UI_LED_B_GPIO_Port, UI_LED_B_Pin, LOW);
}

void LedBOff()
{
    HAL_GPIO_WritePin(UI_LED_B_GPIO_Port, UI_LED_B_Pin, HIGH);
}

void LedBToggle()
{
    HAL_GPIO_TogglePin(UI_LED_B_GPIO_Port, UI_LED_B_Pin);
}

void LedGOn()
{
    HAL_GPIO_WritePin(UI_LED_G_GPIO_Port, UI_LED_G_Pin, LOW);
}

void LedGOff()
{
    HAL_GPIO_WritePin(UI_LED_G_GPIO_Port, UI_LED_G_Pin, HIGH);
}

void LedGToggle()
{
    HAL_GPIO_TogglePin(UI_LED_G_GPIO_Port, UI_LED_G_Pin);
}

void LedsOn()
{
    LedROn();
    LedBOn();
    LedGOn();
}

void LedsOff()
{
    LedROff();
    LedBOff();
    LedGOff();
}

void LedsToggle()
{
    LedRToggle();
    LedBToggle();
    LedGToggle();
}
