Quicr/hactar/firmware/ui/src/link_packet_handler.cc

#include "link_packet_handler.hh"
#include "audio_chip.hh"
#include "audio_codec.hh"
#include "keyboard_display.hh"
#include "link_packet_t.hh"
#include "logger.hh"
#include "stack_debug.hh"
#include "ui_mgmt_link.h"
#include "ui_net_link.hh"
#include <cstdint>
#include <cstdio>
#include <span>

static void HandleAiResponse(link_packet_t* packet, AudioChip& audio)
{
    auto* response =
        static_cast<ui_net_link::AIResponseChunk*>(static_cast<void*>(packet->payload.data() + 1));

    switch (response->content_type)
    {
    case ui_net_link::ContentType::Audio:
    {
        const uint16_t len = constants::Audio_Phonic_Sz < response->chunk_length
                               ? constants::Audio_Phonic_Sz
                               : response->chunk_length;

        AudioCodec::ALawExpand(response->chunk_data, len, audio.HpOutPtr(),
                               constants::Audio_Buffer_Sz, constants::Stereo, true);
        break;
    }
    case ui_net_link::ContentType::Json:
    {
        response->chunk_data[response->chunk_length] = 0;
        UI_LOG_INFO("[AI] %s", response->chunk_data);
        break;
    }
    }
}

void ForwardToMgmt(Serial& mgmt_serial, link_packet_t* packet, const bool last)
{
    static bool first = true;

    if (first)
    {
        first = false;
        mgmt_serial.Reply(static_cast<uint16_t>(UiToCtl::AudioStart), std::span<const uint8_t>{});
    }

    packet->type = static_cast<uint16_t>(UiToCtl::AudioFrameUnprotected);

    mgmt_serial.Write(*packet);

    if (last)
    {
        first = true;
        mgmt_serial.Reply(static_cast<uint16_t>(UiToCtl::AudioEnd), std::span<const uint8_t>{});
    }
}

void HandleQuicrPackets(Serial& mgmt_serial,
                        Protector& protector,
                        AudioChip& audio,
                        const AudioReceiveMode audio_receive_mode,
                        link_packet_t* packet)
{
    // Send to mgmt, and then handle locally
    if (!protector.TryUnprotect(packet))
    {
        UI_LOG_ERROR("Failed to decrypt ptt object");
        return;
    }

    const auto message_type = static_cast<ui_net_link::MessageType>(packet->payload[1]);

    switch (message_type)
    {
    case ui_net_link::MessageType::Media:
    {
        ui_net_link::Chunk* audio_chunk =
            static_cast<ui_net_link::Chunk*>(static_cast<void*>(packet->payload.data() + 1));

        switch (audio_receive_mode)
        {
        case AudioReceiveMode::Ctl:
        {
            ForwardToMgmt(mgmt_serial, packet, audio_chunk->last_chunk);
            break;
        }
        case AudioReceiveMode::Both:
        {
            ForwardToMgmt(mgmt_serial, packet, audio_chunk->last_chunk);
            AudioCodec::ALawExpand(audio_chunk->chunk_data, constants::Audio_Phonic_Sz,
                                   audio.HpOutPtr(), constants::Audio_Buffer_Sz, constants::Stereo,
                                   true);
            break;
        }
        case AudioReceiveMode::Headphones:
        {
            AudioCodec::ALawExpand(audio_chunk->chunk_data, constants::Audio_Phonic_Sz,
                                   audio.HpOutPtr(), constants::Audio_Buffer_Sz, constants::Stereo,
                                   true);
            break;
        }
        default:
        {
            return;
        }
        }
        break;
    }
    case ui_net_link::MessageType::AIRequest:
    {
        break;
    }
    case ui_net_link::MessageType::AIResponse:
    {
        HandleAiResponse(packet, audio);
        break;
    }
    case ui_net_link::MessageType::Chat:
    {
        // HandleChatMessages(screen, packet);
        break;
    }
    default:
    {
        UI_LOG_INFO("Got an unknown message type %d", (int)message_type);
        break;
    }
    }
}

void HandleNetLinkPackets(Serial& net_serial,
                          Serial& mgmt_serial,
                          Protector& protector,
                          AudioChip& audio,
                          const AudioReceiveMode audio_receive_mode)
{
    while (true)
    {
        link_packet_t* packet = net_serial.Read();
        if (!packet)
        {
            return;
        }

        switch (static_cast<ui_net_link::NetToUi>(packet->type))
        {
        case ui_net_link::NetToUi::CircularPing:
        {
            // Forward to MGMT for circular path: MGMT -> NET -> UI -> MGMT
            mgmt_serial.Reply(static_cast<uint16_t>(UiToCtl::CircularPing),
                              std::span<const uint8_t>(packet->payload.data(), packet->length));
            break;
        }
        case ui_net_link::NetToUi::AudioFrame:
        {
            HandleQuicrPackets(mgmt_serial, protector, audio, audio_receive_mode, packet);
            break;
        }
        default:
        {
            UI_LOG_ERROR("Unhandled packet type %d", (int)packet->type);
            break;
        }
        }
    }
}

void HandleMgmtLinkPackets(Serial& mgmt_serial,
                           Serial& net_serial,
                           ConfigStorage& storage,
                           AudioChip& audio_chip,
                           UiLoopbackMode& loopback,
                           AudioTransmitMode& audio_transmit_mode,
                           AudioReceiveMode& audio_receive_mode)
{
    while (true)
    {
        link_packet_t* packet = mgmt_serial.Read();
        if (!packet)
        {
            break;
        }

        switch (static_cast<CtlToUi>(packet->type))
        {
        case CtlToUi::Ping:
        {
            if (packet->length > 0)
            {
                mgmt_serial.Reply(static_cast<uint16_t>(UiToCtl::Pong),
                                  std::span<const uint8_t>(packet->payload.data(), packet->length));
            }
            else
            {
                mgmt_serial.Reply(static_cast<uint16_t>(UiToCtl::Pong), std::span<const uint8_t>{});
            }
            break;
        }
        case CtlToUi::CircularPing:
        {
            // Forward to NET for circular path: MGMT -> UI -> NET -> MGMT
            net_serial.Reply(static_cast<uint16_t>(ui_net_link::UiToNet::CircularPing),
                             std::span<const uint8_t>(packet->payload.data(), packet->length));
            break;
        }
        case CtlToUi::GetVersion:
        {
            uint32_t version = storage.GetVersion();
            uint8_t buf[4];
            buf[0] = static_cast<uint8_t>((version >> 24) & 0xFF);
            buf[1] = static_cast<uint8_t>((version >> 16) & 0xFF);
            buf[2] = static_cast<uint8_t>((version >> 8) & 0xFF);
            buf[3] = static_cast<uint8_t>(version & 0xFF);
            mgmt_serial.Reply(static_cast<uint16_t>(UiToCtl::Version),
                              std::span<const uint8_t>(buf, 4));
            break;
        }
        case CtlToUi::SetVersion:
        {
            if (packet->length != 4)
            {
                UI_LOG_ERROR("ERR. Version must be 4 bytes");
                mgmt_serial.ReplyError(static_cast<uint16_t>(UiToCtl::Error),
                                       "Version must be 4 bytes");
                break;
            }
            uint32_t version = (static_cast<uint32_t>(packet->payload[0]) << 24)
                             | (static_cast<uint32_t>(packet->payload[1]) << 16)
                             | (static_cast<uint32_t>(packet->payload[2]) << 8)
                             | static_cast<uint32_t>(packet->payload[3]);
            if (storage.SetVersion(version))
            {
                UI_LOG_INFO("OK! Version set to 0x%08lx", version);
                mgmt_serial.Reply(static_cast<uint16_t>(UiToCtl::Ack), std::span<const uint8_t>{});
            }
            else
            {
                UI_LOG_ERROR("ERR. Failed to set version");
                mgmt_serial.ReplyError(static_cast<uint16_t>(UiToCtl::Error),
                                       "Failed to set version");
            }
            break;
        }
        case CtlToUi::GetSframeKey:
        {
            ConfigStorage::Config config = storage.Load(ConfigStorage::Config_Id::Sframe_Key);
            if (config.loaded && config.len == 16)
            {
                mgmt_serial.Reply(static_cast<uint16_t>(UiToCtl::SframeKey),
                                  std::span<const uint8_t>(config.buff, config.len));
            }
            else
            {
                mgmt_serial.ReplyError(static_cast<uint16_t>(UiToCtl::Error),
                                       "SFrame key not found");
            }
            break;
        }
        case CtlToUi::SetSframeKey:
        {
            if (packet->length != 16)
            {
                UI_LOG_ERROR("ERR. Sframe key must be 16 bytes");
                mgmt_serial.ReplyError(static_cast<uint16_t>(UiToCtl::Error),
                                       "SFrame key must be 16 bytes");
                break;
            }

            if (storage.Save(ConfigStorage::Config_Id::Sframe_Key, packet->payload.data(),
                             packet->length))
            {
                UI_LOG_INFO("OK! Saved SFrame Key configuration");
                mgmt_serial.Reply(static_cast<uint16_t>(UiToCtl::Ack), std::span<const uint8_t>{});
            }
            else
            {
                UI_LOG_ERROR("ERR. Failed to save SFrame Key configuration");
                mgmt_serial.ReplyError(static_cast<uint16_t>(UiToCtl::Error),
                                       "Failed to save SFrame key");
            }
            break;
        }
        case CtlToUi::GetLoopback:
        {
            uint8_t mode = static_cast<uint8_t>(loopback);
            mgmt_serial.Reply(static_cast<uint16_t>(UiToCtl::Loopback),
                              std::span<const uint8_t>(&mode, 1));
            break;
        }
        case CtlToUi::SetLoopback:
        {
            if (packet->length < 1)
            {
                mgmt_serial.ReplyError(static_cast<uint16_t>(UiToCtl::Error),
                                       "Missing loopback mode parameter");
                break;
            }

            const uint8_t mode = packet->payload[0];

            if (mode >= static_cast<uint8_t>(UiLoopbackMode::Count))
            {
                mgmt_serial.ReplyError(static_cast<uint16_t>(UiToCtl::Error),
                                       "Loopback mode given is not supported");
                return;
            }

            loopback = static_cast<UiLoopbackMode>(mode);

            mgmt_serial.Reply(static_cast<uint16_t>(UiToCtl::Ack), std::span<const uint8_t>{});

            break;
        }
        case CtlToUi::GetStackInfo:
        {
            stack_debug::StackInfo info = stack_debug::GetStackInfo();
            char json[128];
            int len = snprintf(
                json, sizeof(json),
                "{\"stack_base\":%lu,\"stack_top\":%lu,\"stack_size\":%lu,\"stack_used\":%lu}",
                info.stack_base, info.stack_top, info.stack_size, info.stack_used);
            mgmt_serial.Reply(
                static_cast<uint16_t>(UiToCtl::StackInfo),
                std::span<const uint8_t>(reinterpret_cast<const uint8_t*>(json), len));
            break;
        }
        case CtlToUi::RepaintStack:
        {
            stack_debug::RepaintStack();
            mgmt_serial.Reply(static_cast<uint16_t>(UiToCtl::Ack), std::span<const uint8_t>{});
            break;
        }
        case CtlToUi::GetLogsEnabled:
        {
            uint8_t enabled = Logger::enabled ? 1 : 0;
            mgmt_serial.Reply(static_cast<uint16_t>(UiToCtl::LogsEnabled),
                              std::span<const uint8_t>(&enabled, 1));
            break;
        }
        case CtlToUi::SetLogsEnabled:
        {
            if (packet->length < 1)
            {
                mgmt_serial.ReplyError(static_cast<uint16_t>(UiToCtl::Error),
                                       "Missing logs enabled parameter");
                break;
            }
            const uint8_t enabled = packet->payload[0];
            if (enabled)
            {
                Logger::Enable();
            }
            else
            {
                Logger::Disable();
            }
            mgmt_serial.Reply(static_cast<uint16_t>(UiToCtl::Ack), std::span<const uint8_t>{});
            break;
        }
        case CtlToUi::ClearStorage:
        {
            UI_LOG_INFO("OK! Clearing configurations");
            storage.Clear();
            UI_LOG_INFO("OK! Cleared all configurations");
            mgmt_serial.Reply(static_cast<uint16_t>(UiToCtl::Ack), std::span<const uint8_t>{});
            break;
        }
        case CtlToUi::GetVolume:
        {
            UI_LOG_INFO("Get volume");
            const uint8_t curr_vol = audio_chip.DACVolume();
            mgmt_serial.Reply(static_cast<uint16_t>(UiToCtl::Volume),
                              std::span<const uint8_t>(&curr_vol, 1));
            break;
        }
        case CtlToUi::SetVolume:
        {
            UI_LOG_INFO("Set volume");
            if (packet->length < 1)
            {
                mgmt_serial.ReplyError(static_cast<uint16_t>(UiToCtl::Error),
                                       "Missing set volume parameter");
                break;
            }

            const uint16_t volume = static_cast<uint16_t>(packet->payload[0]);

            audio_chip.DACVolumeSet(volume);

            const uint8_t curr_vol = audio_chip.DACVolume();
            mgmt_serial.Reply(static_cast<uint16_t>(UiToCtl::Volume),
                              std::span<const uint8_t>(&curr_vol, 1));
            break;
        }
        case CtlToUi::AdjVolume:
        {
            if (packet->length < 2)
            {
                mgmt_serial.ReplyError(static_cast<uint16_t>(UiToCtl::Error),
                                       "Missing adj volume parameter");
            }

            const AudioAdjustDirection direction =
                static_cast<AudioAdjustDirection>(packet->payload[0]);

            const int8_t amt = static_cast<int8_t>(packet->payload[1]);

            switch (direction)
            {
            case AudioAdjustDirection::Down:
            {
                audio_chip.DACVolumeAdjust(-amt);
                break;
            }
            case AudioAdjustDirection::Up:
            {
                audio_chip.DACVolumeAdjust(amt);
                break;
            }
            default:
            {
                mgmt_serial.ReplyError(static_cast<uint16_t>(UiToCtl::Error),
                                       "Direction parameter is not equal to 0 or 1");
                return;
            }
            }

            const uint8_t curr_vol = audio_chip.DACVolume();
            mgmt_serial.Reply(static_cast<uint16_t>(UiToCtl::Volume),
                              std::span<const uint8_t>(&curr_vol, 1));
            break;
        }
        case CtlToUi::GetMicPreamp:
        {
            UI_LOG_INFO("Get ADC Volume");
            const uint8_t mic_preamp = audio_chip.ADCVolume();
            mgmt_serial.Reply(static_cast<uint16_t>(UiToCtl::MicPreamp),
                              std::span<const uint8_t>(&mic_preamp, 1));
            break;
        }
        case CtlToUi::SetMicPreamp:
        {
            UI_LOG_INFO("Set ADC Volume");
            if (packet->length < 1)
            {
                mgmt_serial.ReplyError(static_cast<uint16_t>(UiToCtl::Error),
                                       "Missing set volume parameter");
                break;
            }

            const uint8_t set_mic_preamp = packet->payload[0];

            audio_chip.ADCVolumeSet(set_mic_preamp);

            const uint8_t mic_preamp = audio_chip.ADCVolume();
            mgmt_serial.Reply(static_cast<uint16_t>(UiToCtl::MicPreamp),
                              std::span<const uint8_t>(&mic_preamp, 1));
            break;
        }
        case CtlToUi::AdjMicPreamp:
        {
            UI_LOG_INFO("Micpreamp up/down");
            if (packet->length < 2)
            {
                mgmt_serial.ReplyError(static_cast<uint16_t>(UiToCtl::Error),
                                       "Missing adj mic-preamp parameter");
                break;
            }

            const AudioAdjustDirection direction =
                static_cast<AudioAdjustDirection>(packet->payload[0]);

            const int8_t amt = static_cast<int8_t>(packet->payload[1]);

            switch (direction)
            {
            case AudioAdjustDirection::Down:
            {
                audio_chip.ADCVolumeAdjust(-amt);
                break;
            }
            case AudioAdjustDirection::Up:
            {
                audio_chip.ADCVolumeAdjust(amt);
                break;
            }
            default:
            {
                mgmt_serial.ReplyError(static_cast<uint16_t>(UiToCtl::Error),
                                       "Direction parameter is not equal to 0 or 1");
                return;
            }
            }

            const uint8_t mic_preamp = audio_chip.ADCVolume();
            mgmt_serial.Reply(static_cast<uint16_t>(UiToCtl::MicPreamp),
                              std::span<const uint8_t>(&mic_preamp, 1));
            break;
        }
        case CtlToUi::GetAudioTransmitMode:
        {
            UI_LOG_INFO("Mgmt requested audio transmit mode");
            const uint8_t tmp = static_cast<const uint8_t>(audio_transmit_mode);
            mgmt_serial.Reply(static_cast<uint16_t>(UiToCtl::AudioTransmitMode),
                              std::span<const uint8_t>(&tmp, 1));
            break;
        }
        case CtlToUi::SetAudioTransmitMode:
        {
            if (packet->length < 1)
            {
                mgmt_serial.ReplyError(static_cast<uint16_t>(UiToCtl::Error),
                                       "Missing set audio transmit mode parameter");
                break;
            }

            audio_transmit_mode = static_cast<AudioTransmitMode>(packet->payload[0]);
            mgmt_serial.Reply(static_cast<uint16_t>(UiToCtl::Ack), std::span<const uint8_t>{});

            break;
        }
        case CtlToUi::GetAudioReceiveMode:
        {
            UI_LOG_INFO("Mgmt requested audio receive mode");
            const uint8_t tmp = static_cast<const uint8_t>(audio_receive_mode);
            mgmt_serial.Reply(static_cast<uint16_t>(UiToCtl::AudioReceiveMode),
                              std::span<const uint8_t>(&tmp, 1));
            break;
        }
        case CtlToUi::SetAudioReceiveMode:
        {
            if (packet->length < 1)
            {
                mgmt_serial.ReplyError(static_cast<uint16_t>(UiToCtl::Error),
                                       "Missing set audio recieve mode parameter");
                break;
            }

            audio_receive_mode = static_cast<AudioReceiveMode>(packet->payload[0]);
            mgmt_serial.Reply(static_cast<uint16_t>(UiToCtl::Ack), std::span<const uint8_t>{});

            break;
        }
        case CtlToUi::AudioFrame:
        {
            if (packet->length < sizeof(ui_net_link::Chunk::ExpectedSize))
            {
                mgmt_serial.ReplyError(static_cast<uint16_t>(UiToCtl::Error),
                                       "Audio frame is the wrong size");
                break;
            }

            ui_net_link::Chunk* audio_chunk =
                static_cast<ui_net_link::Chunk*>(static_cast<void*>(packet->payload.data() + 1));
            AudioCodec::ALawExpand(audio_chunk->chunk_data, constants::Audio_Phonic_Sz,
                                   audio_chip.HpOutPtr(), constants::Audio_Buffer_Sz,
                                   constants::Stereo, true);
            break;
        }
        case CtlToUi::AudioStart:
        {
            break;
        }
        default:
        {
            UI_LOG_ERROR("ERR. No handler for packet type 0x%04x", packet->type);
            break;
        }
        }
    }
}
