Quicr/hactar/firmware/ui/dependencies/cmox/include/ecc/cmox_eddsa.h

/**
  ******************************************************************************
  * @file    cmox_eddsa.h
  * @author  MCD Application Team
  * @brief   Header file for EdDSA signature creation and verification
  ******************************************************************************
  * @attention
  *
  * Copyright (c) 2021 STMicroelectronics.
  * All rights reserved.
  *
  * This software is licensed under terms that can be found in the LICENSE file
  * in the root directory of this software component.
  * If no LICENSE file comes with this software, it is provided AS-IS.
  *
  ******************************************************************************
  */

#ifndef CMOX_EDDSA_H
#define CMOX_EDDSA_H

#ifdef __cplusplus
extern "C" {
#endif

#include "ecc/cmox_ecc.h"

/** @addtogroup CMOX_ECC
  * @{
  */

/**
  * @defgroup CMOX_ECC_EDDSA EDDSA algorithm
  * @{
  */

/** @defgroup CMOX_ECC_EDDSA_PUBLIC_METHODS EDDSA public method prototypes
  * @{
  */

/**
  * @brief      Generate private and public keys to use with EDDSA
  * @param[in]  P_pEccCtx       Context for ECC operations
  * @param[in]  P_CurveParams   Curve Parameters and point functions
  *                             This parameter can be one of the following:
  *                                @arg CMOX_ECC_ED25519_HIGHMEM
  *                                @arg CMOX_ECC_ED25519_OPT_LOWMEM
  *                                @arg CMOX_ECC_ED25519_OPT_HIGHMEM
  *                                @arg CMOX_ECC_ED448_LOWMEM
  *                                @arg CMOX_ECC_ED448_HIGHMEM
  * @param[in]  P_pRandom       Buffer of random bytes
  * @param[in]  P_RandomLen     Byte length of the random buffer
  * @param[out] P_pPrivKey      Buffer with the private key, whose first half will be the secret value and the second
  *                             half will contain the public key
  * @param[out] P_pPrivKeyLen   Byte length of the private key
  * @param[out] P_pPubKey       Buffer with the public key
  * @param[out] P_pPubKeyLen    Byte length of the public key
  * @note If P_RandomLen is not enough, an error is returned and P_pPrivKeyLen
  *       contains the minimum number of bytes of random to provide (and is also
  *       half the minimum length of P_pPrivKey), while P_pPubKeyLen contains the
  *       minimum length of P_pPubKey.
  * @retval     CMOX_ECC_SUCCESS                Everything OK
  * @retval     CMOX_ECC_ERR_MATHCURVE_MISMATCH Mathematical function set is not compatible with current ECC curve
  * @retval     CMOX_ECC_ERR_ALGOCURVE_MISMATCH Curve is not compatible with current functionality
  * @retval     CMOX_ECC_ERR_BAD_PARAMETERS     Some NULL/wrong/empty parameter or Construct API not called
  * @retval     CMOX_ECC_ERR_WRONG_RANDOM       Random material too short or not valid for the functionality
  * @retval     CMOX_ECC_ERR_MEMORY_FAIL        Not enough memory
  * @retval     CMOX_ECC_ERR_INTERNAL           Something went wrong during internal computations (e.g. hash)
  */
cmox_ecc_retval_t cmox_eddsa_keyGen(cmox_ecc_handle_t     *P_pEccCtx,
                                    const cmox_ecc_impl_t P_CurveParams,
                                    const uint8_t         *P_pRandom,
                                    size_t                P_RandomLen,
                                    uint8_t               *P_pPrivKey,
                                    size_t                *P_pPrivKeyLen,
                                    uint8_t               *P_pPubKey,
                                    size_t                *P_pPubKeyLen);

/**
  * @brief      Generate a signature, using EDDSA
  * @param[in]  P_pEccCtx       Context for ECC operations
  * @param[in]  P_CurveParams   Curve Parameters and point functions
  *                             This parameter can be one of the following:
  *                                @arg CMOX_ECC_ED25519_HIGHMEM
  *                                @arg CMOX_ECC_ED25519_OPT_LOWMEM
  *                                @arg CMOX_ECC_ED25519_OPT_HIGHMEM
  *                                @arg CMOX_ECC_ED448_LOWMEM
  *                                @arg CMOX_ECC_ED448_HIGHMEM
  * @param[in]  P_pPrivKey      Buffer with the private key, whose first half is the secret value and the second half
  *                             contains the public key
  * @param[in]  P_PrivKeyLen    Byte length of the private key
  * @param[in]  P_pMessage      Buffer with the message to sign
  * @param[in]  P_MessageLen    Byte length of the message
  * @param[out] P_pSignature    Buffer with the signature (concatenation of R and S)
  * @param[out] P_pSignatureLen Byte length of the signature
  * @retval     CMOX_ECC_SUCCESS                Everything OK
  * @retval     CMOX_ECC_ERR_MATHCURVE_MISMATCH Mathematical function set is not compatible with current ECC curve
  * @retval     CMOX_ECC_ERR_ALGOCURVE_MISMATCH Curve is not compatible with current functionality
  * @retval     CMOX_ECC_ERR_BAD_PARAMETERS     Some NULL/wrong/empty parameter or Construct API not called
  * @retval     CMOX_ECC_ERR_MEMORY_FAIL        Not enough memory
  * @retval     CMOX_ECC_ERR_INTERNAL           Something went wrong during internal computations (e.g. hash)
  */
cmox_ecc_retval_t cmox_eddsa_sign(cmox_ecc_handle_t     *P_pEccCtx,
                                  const cmox_ecc_impl_t P_CurveParams,
                                  const uint8_t         *P_pPrivKey,
                                  size_t                P_PrivKeyLen,
                                  const uint8_t         *P_pMessage,
                                  size_t                P_MessageLen,
                                  uint8_t               *P_pSignature,
                                  size_t                *P_pSignatureLen);

/**
  * @brief      Verify a signature, using EDDSA
  * @param[in]  P_pEccCtx       Context for ECC operations
  * @param[in]  P_CurveParams   Curve Parameters and point functions
  *                             This parameter can be one of the following:
  *                                @arg CMOX_ECC_ED25519_HIGHMEM
  *                                @arg CMOX_ECC_ED25519_OPT_LOWMEM
  *                                @arg CMOX_ECC_ED25519_OPT_HIGHMEM
  *                                @arg CMOX_ECC_ED448_LOWMEM
  *                                @arg CMOX_ECC_ED448_HIGHMEM
  * @param[in]  P_pPubKey       Buffer with the public key
  * @param[in]  P_PubKeyLen     Byte length of the public key
  * @param[in]  P_pMessage      Buffer with the message to verify
  * @param[in]  P_MessageLen    Byte length of the message
  * @param[in]  P_pSignature    Buffer with the signature (concatenation of R and S)
  * @param[in]  P_SignatureLen  Byte length of the signature
  * @param[out] P_pFaultCheck   Optional value to check, together with the retval, to verify if some fault happened
  * @retval     CMOX_ECC_AUTH_SUCCESS           Signature verified
  * @retval     CMOX_ECC_AUTH_FAIL              Signature NOT verified
  * @retval     CMOX_ECC_ERR_MATHCURVE_MISMATCH Mathematical function set is not compatible with current ECC curve
  * @retval     CMOX_ECC_ERR_ALGOCURVE_MISMATCH Curve is not compatible with current functionality
  * @retval     CMOX_ECC_ERR_BAD_PARAMETERS     Some NULL/wrong/empty parameter or Construct API not called
  * @retval     CMOX_ECC_ERR_MEMORY_FAIL        Not enough memory
  * @retval     CMOX_ECC_ERR_INTERNAL           Something went wrong during internal computations (e.g. hash)
  * @retval     CMOX_ECC_ERR_INVALID_SIGNATURE  Input signature corrupted or not in the expected format
  * @retval     CMOX_ECC_ERR_INVALID_PUBKEY     Public key not in a valid format
  * @note       P_pFaultCheck value, if the parameter is provided, MUST be checked to
  *             be equal to the retval, and both MUST be equal to the successful value.
  *             P_pFaultCheck MUST be checked only if the main result is successful,
  *             and has no relevance if the main result is not successful.
  *             Every comparison (both for the return value and for P_pFaultCheck) must be done against
  *             the success value, and not comparing the value with the failure value. Indeed, in presence of faults,
  *             especially P_pFaultCheck, could be a dirty value.
  */
cmox_ecc_retval_t cmox_eddsa_verify(cmox_ecc_handle_t     *P_pEccCtx,
                                    const cmox_ecc_impl_t P_CurveParams,
                                    const uint8_t         *P_pPubKey,
                                    size_t                P_PubKeyLen,
                                    const uint8_t         *P_pMessage,
                                    size_t                P_MessageLen,
                                    const uint8_t         *P_pSignature,
                                    size_t                P_SignatureLen,
                                    uint32_t              *P_pFaultCheck);

/**
  * @}
  */

/**
  * @}
  */

/**
  * @}
  */

#ifdef __cplusplus
}
#endif

#endif /* CMOX_EDDSA_H */


/************************ (C) COPYRIGHT STMicroelectronics *****END OF FILE****/
