Quicr/hactar/firmware/net/core/src/ui_link_handler.cc

#include "ui_link_handler.hh"
#include "net.hh"
#include "net_mgmt_link.h"
#include "ui_net_link.hh"

UiLinkHandler::UiLinkHandler(Serial& ui_layer,
                             Serial& mgmt_layer,
                             MoqContext& moq_context,
                             const Runtime& runtime,
                             const Diagnostics& diagnostics) :
    ui_layer(ui_layer),
    mgmt_layer(mgmt_layer),
    moq_context(moq_context),
    runtime(runtime),
    diagnostics(diagnostics),
    read_handle(nullptr),
    read_buffer(),
    read_stack(),
    read_semaphore(nullptr),
    read_running(false)
{
}

UiLinkHandler::~UiLinkHandler()
{
    read_running = false;

    if (read_handle)
    {
        // Tell the task to wake up so it can be stopped
        xTaskNotifyGive(read_handle);
        xSemaphoreTake(read_semaphore, portMAX_DELAY);
        read_handle = nullptr;
    }

    if (read_semaphore)
    {
        vSemaphoreDelete(read_semaphore);
        read_semaphore = nullptr;
    }

    if (read_stack)
    {
        heap_caps_free(read_stack);
        read_stack = nullptr;
    }
}

void UiLinkHandler::Begin()
{
    CreateLinkPacketTask();
    ui_layer.BeginEventTask(read_handle);
}

void UiLinkHandler::CreateLinkPacketTask()
{
    NET_LOG_INFO("Creating ui link packet task");

    read_semaphore = xSemaphoreCreateBinary();
    if (read_semaphore == NULL)
    {
        esp_system_abort("Failed to allocate semaphore for mgmt link packet handler");
        return;
    }

    read_stack =
        (StackType_t*)heap_caps_malloc(Stack_Size * sizeof(StackType_t), MALLOC_CAP_INTERNAL);
    if (read_stack == NULL)
    {
        esp_system_abort("Failed to allocate stack for mgmt link packet handler");
        return;
    }

    read_running = true;
    read_handle = xTaskCreateStatic(LinkPacketTask, "mgmt link packet handler", Stack_Size, this,
                                    10, read_stack, &read_buffer);

    NET_LOG_INFO("Created mgmt link packet handler Internal RAM left %ld",
                 heap_caps_get_free_size(MALLOC_CAP_INTERNAL));
}

void UiLinkHandler::LinkPacketTask(void* arg)
{
    UiLinkHandler* handler = static_cast<UiLinkHandler*>(arg);

    NET_LOG_INFO("Start ui link packet task");
    while (handler->read_running)
    {
        ulTaskNotifyTake(pdTRUE, portMAX_DELAY);

        while (auto packet = handler->ui_layer.Read())
        {
            if (packet->type == static_cast<uint16_t>(ui_net_link::UiToNet::CircularPing))
            {
                // Forward to MGMT for circular path: MGMT -> UI -> NET -> MGMT
                handler->mgmt_layer.Reply(
                    static_cast<uint16_t>(NetToCtl::CircularPing),
                    std::span<const uint8_t>(packet->payload.data(), packet->length));
                continue;
            }

            if (packet->type != static_cast<uint16_t>(ui_net_link::UiToNet::AudioFrame))
            {
                NET_LOG_ERROR("Got unexpected packet type %d", (int)packet->type);
                continue;
            }

            if (packet->length < 1)
            {
                NET_LOG_ERROR("Got audio frame without channel id");
                continue;
            }

            switch (handler->diagnostics.loopback)
            {
            case NetLoopbackMode::Raw:
            {
                packet->type = static_cast<uint16_t>(ui_net_link::NetToUi::AudioFrame);
                handler->ui_layer.Write(*packet);
                break;
            }
            case NetLoopbackMode::Off:
                [[fallthrough]];
            case NetLoopbackMode::Moq:
            {
                const uint8_t channel_id = packet->payload[0];
                const uint32_t length = packet->length - 1;
                handler->moq_context.PushAudioFrame(channel_id, packet->payload.data() + 1, length,
                                                    handler->runtime.curr_audio_isr_time);

                break;
            }
            default:
            {
                NET_LOG_ERROR("LinkPacketTask: Error, unhandled NetLoopbackMode %d",
                              (int)handler->diagnostics.loopback);
                break;
            }
            };
        }
    }
}
